sajeedGIT/shrike_lite_ssm/asset/reddit.png

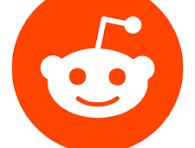
asset/reddit.png
