sajeedGIT/shrike_lite_ssm/asset/shrike_blink.webp

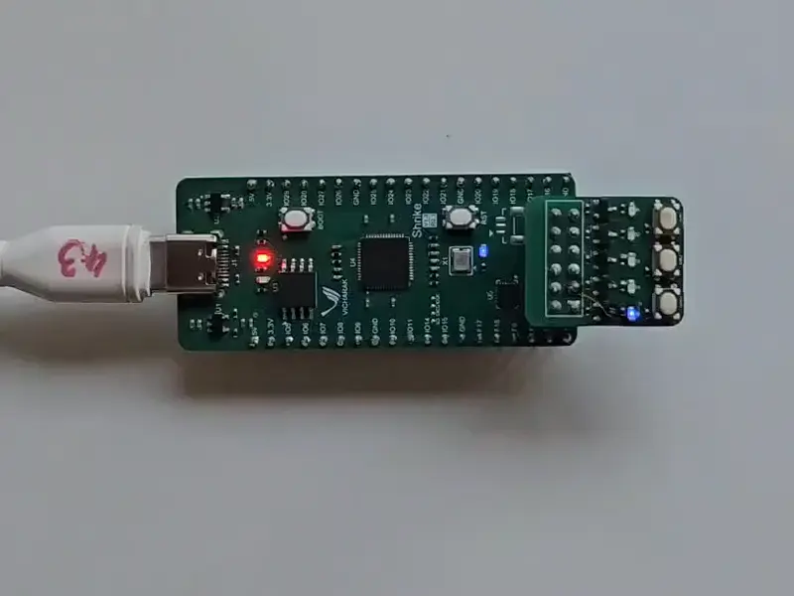
asset/shrike_blink.webp
