sajeedGIT/shrike_lite_ssm/asset/shrike_render.png

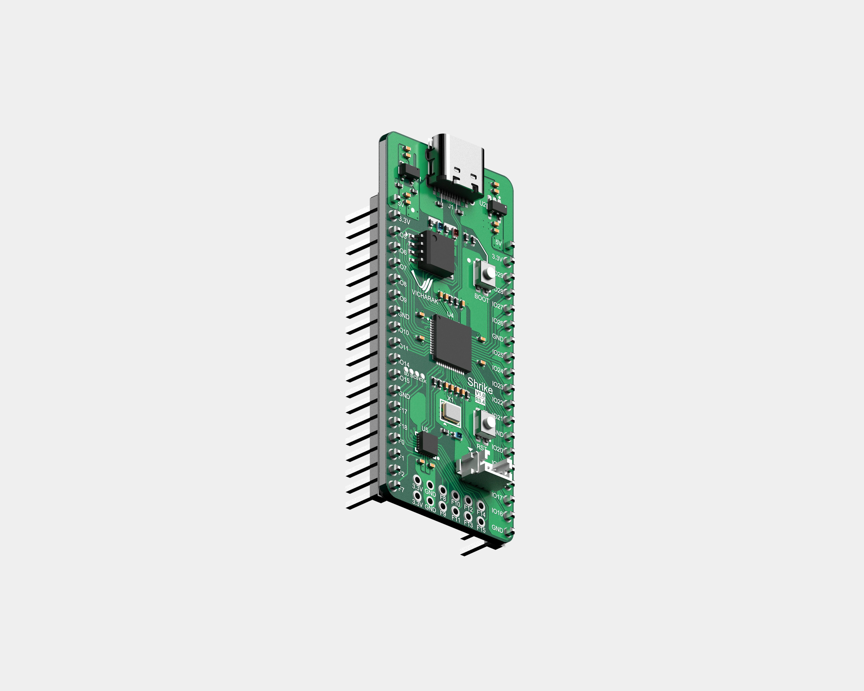
asset/shrike_render.png
