sajeedGIT/shrike_lite_ssm/docs/images/bit_stream.png

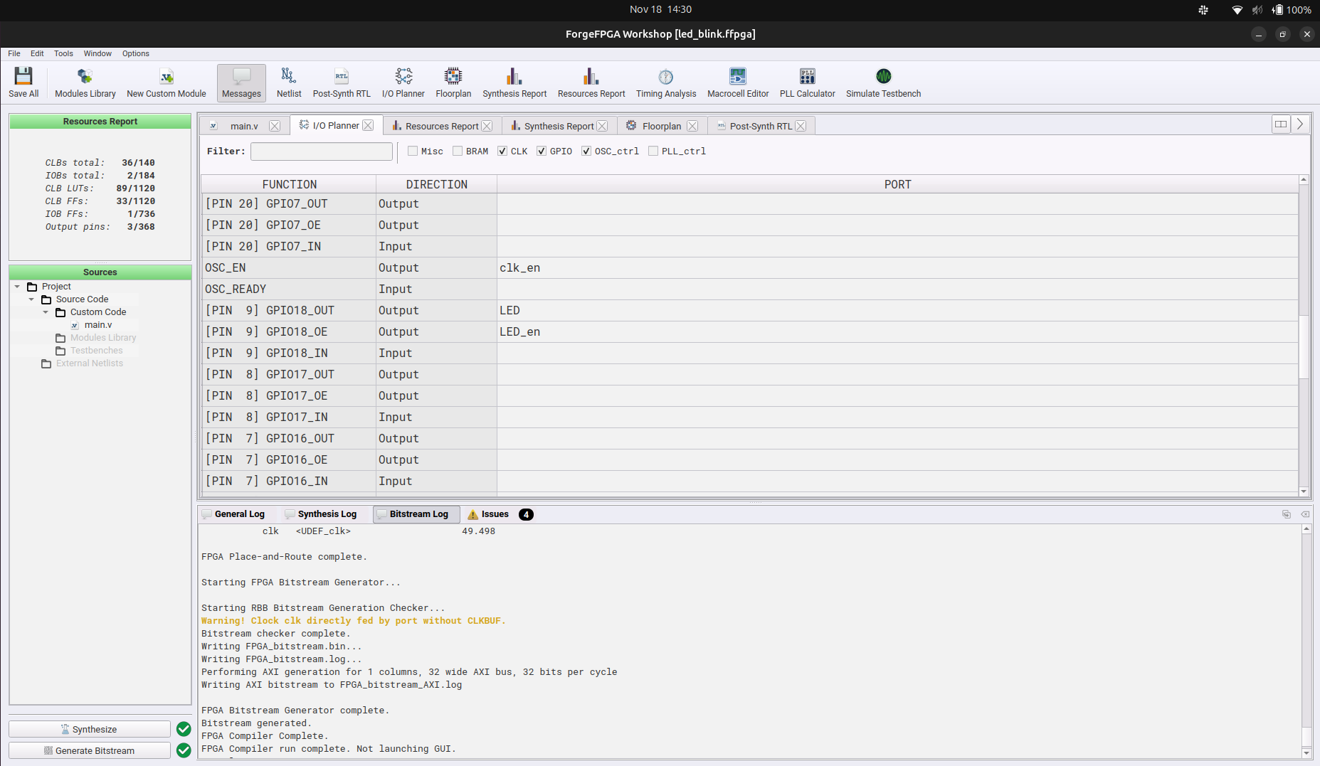
docs/images/bit_stream.png
