sajeedGIT/shrike_lite_ssm/docs/images/bitstream_gen/bitstream_done.png

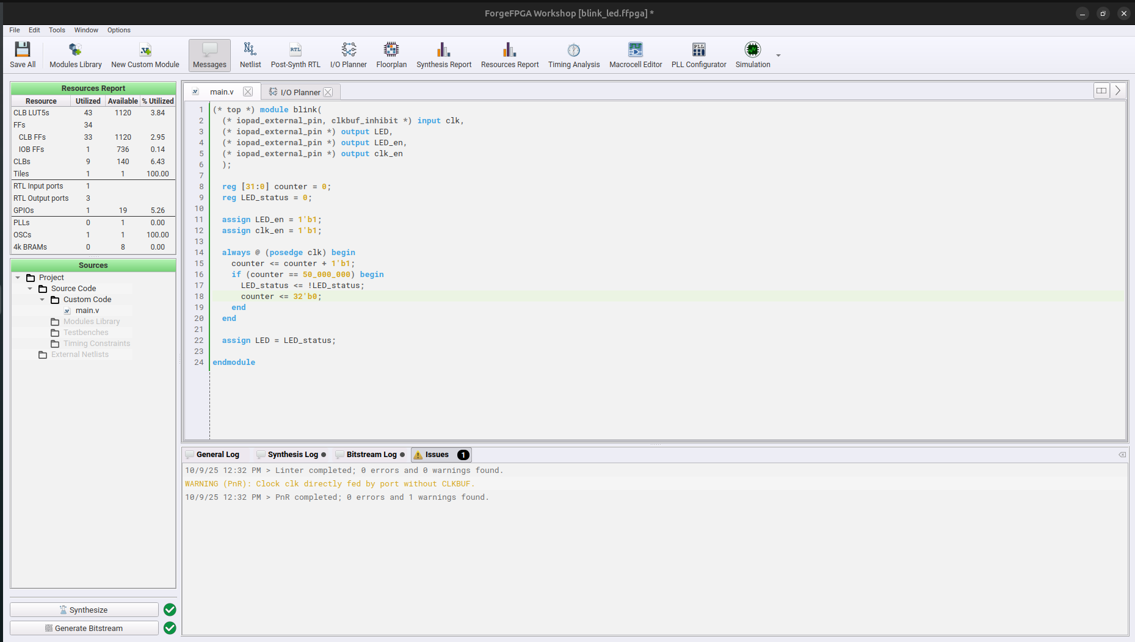
docs/images/bitstream_gen/bitstream_done.png
