sajeedGIT/shrike_lite_ssm/docs/images/bitstream_gen/clk_io.png

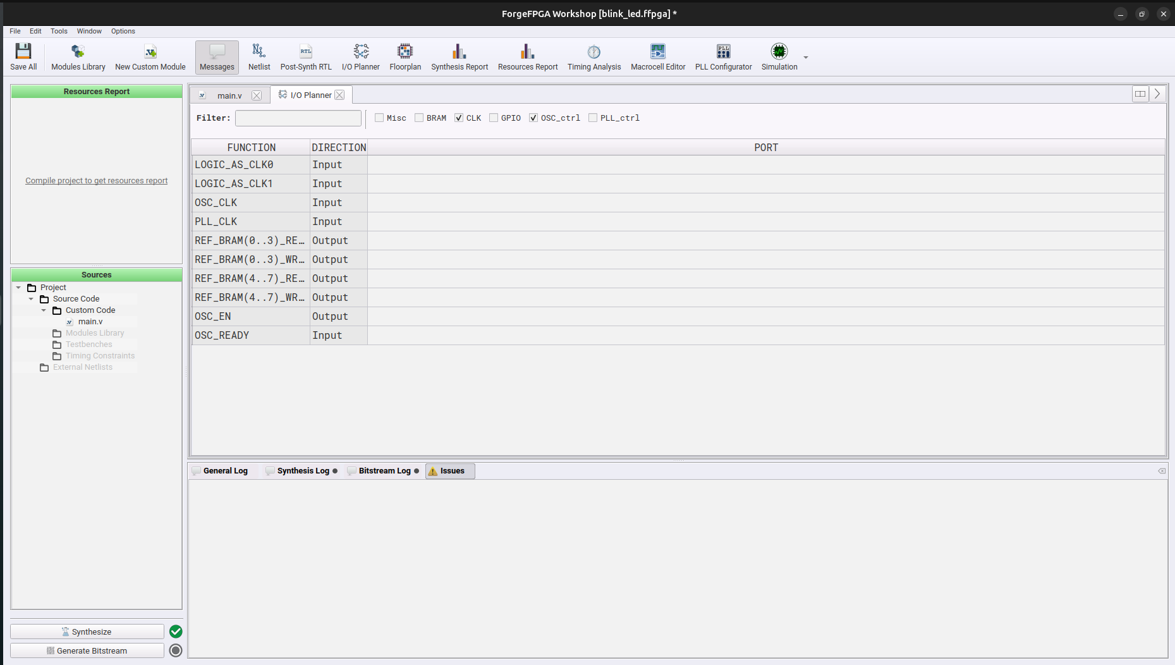
docs/images/bitstream_gen/clk_io.png
