sajeedGIT/shrike_lite_ssm/docs/images/bitstream_gen/empty_main.png

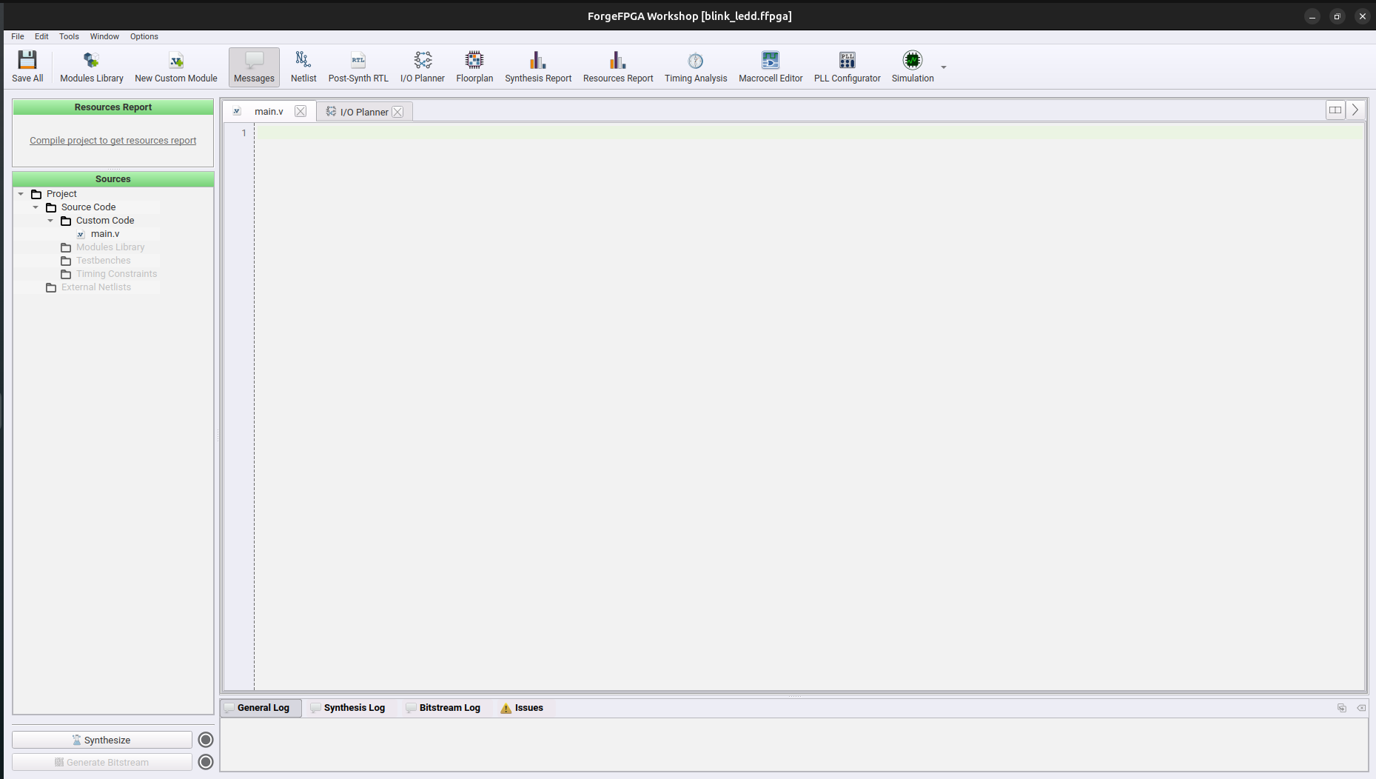
docs/images/bitstream_gen/empty_main.png
