sajeedGIT/shrike_lite_ssm/docs/images/bitstream_gen/fpga_selection.png

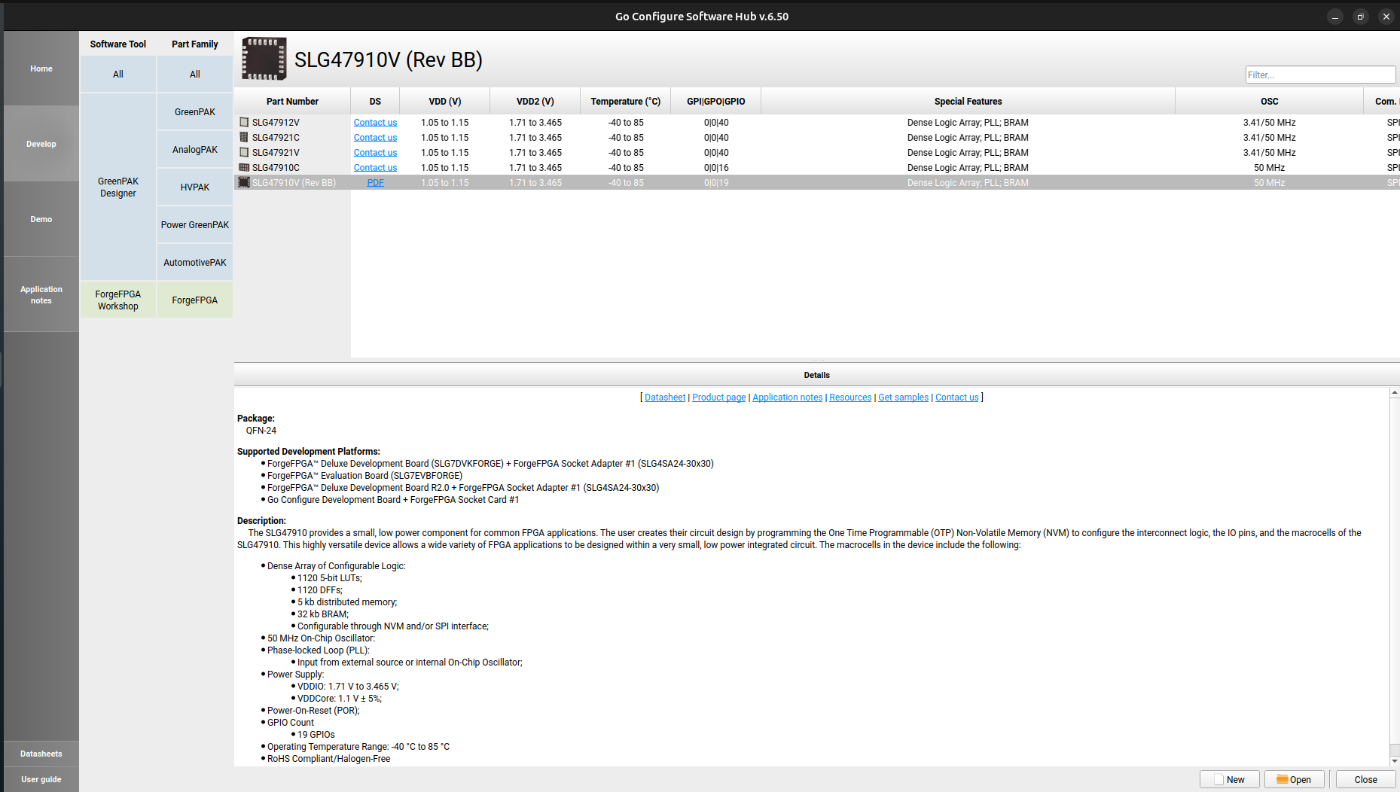
docs/images/bitstream_gen/fpga_selection.png
