sajeedGIT/shrike_lite_ssm/docs/images/bitstream_gen/fpgacore.png

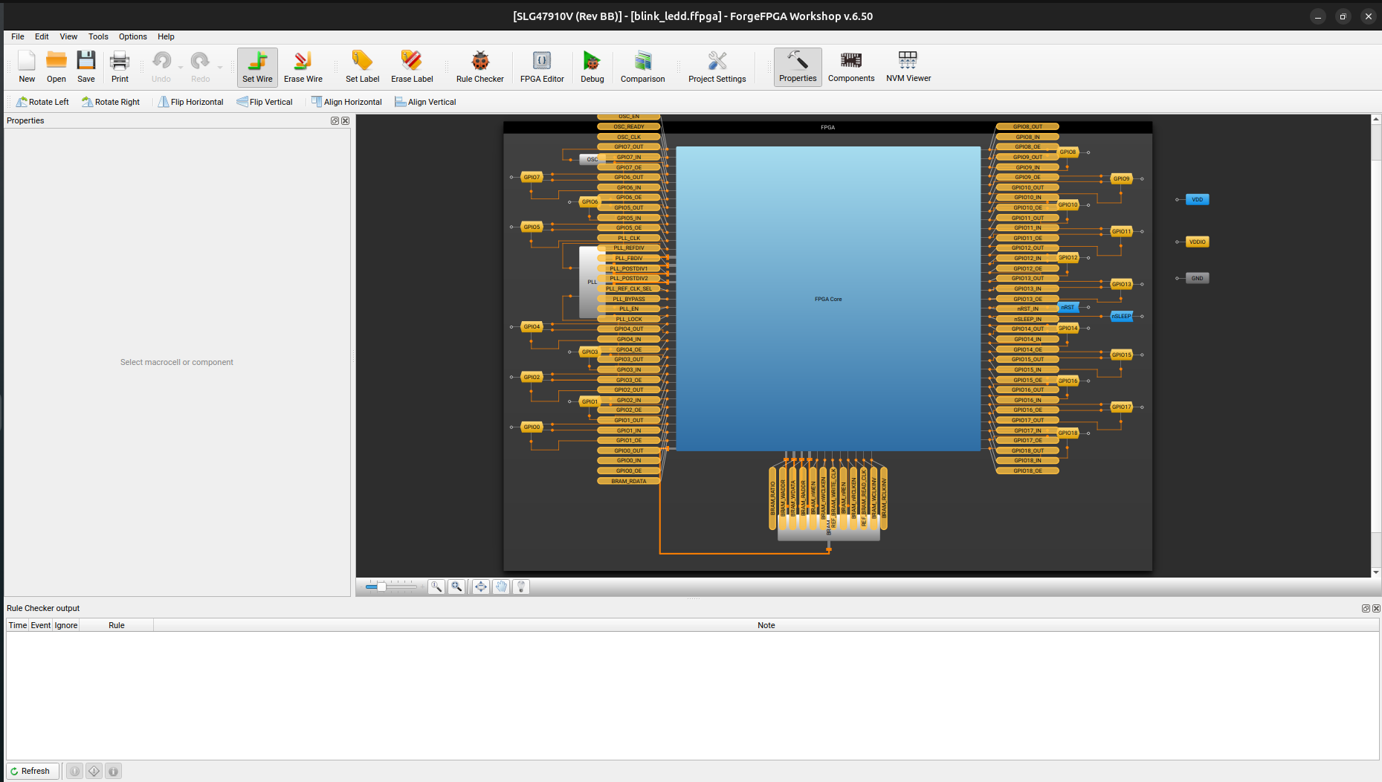
docs/images/bitstream_gen/fpgacore.png
