sajeedGIT/shrike_lite_ssm/docs/images/bitstream_gen/go_config_launch.png

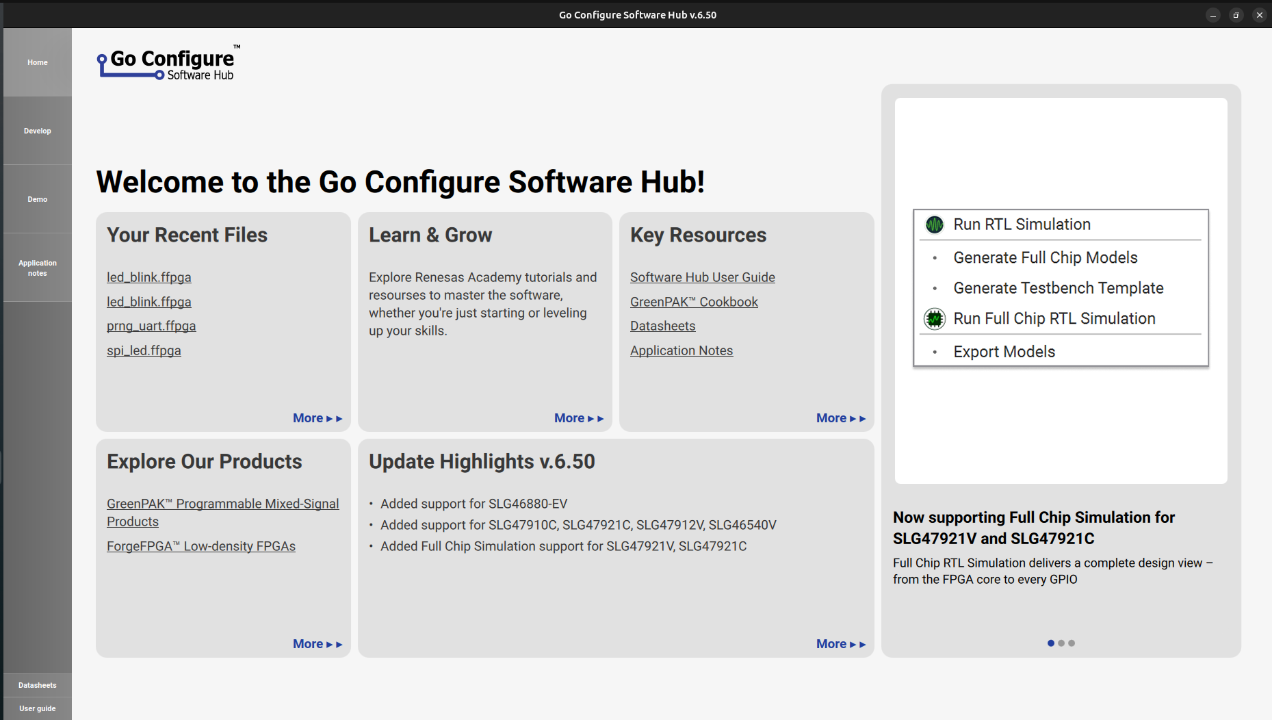
docs/images/bitstream_gen/go_config_launch.png
