sajeedGIT/shrike_lite_ssm/docs/images/bitstream_gen/io_planner.png

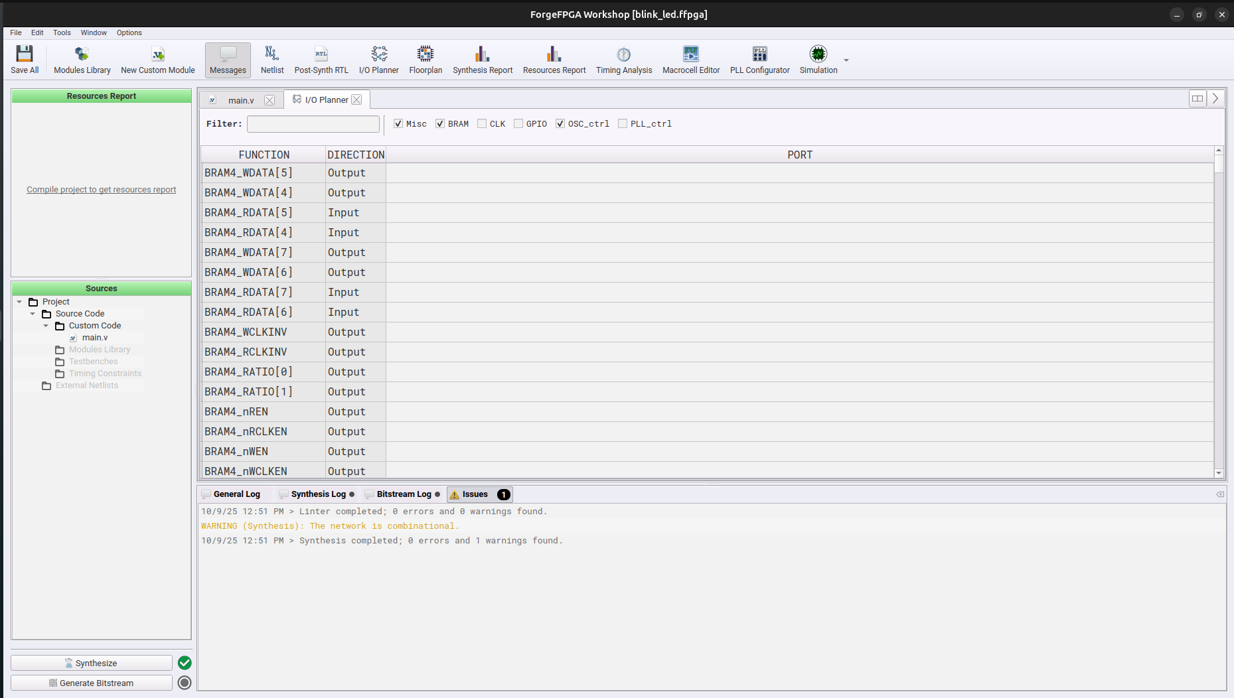
docs/images/bitstream_gen/io_planner.png
