sajeedGIT/shrike_lite_ssm/docs/images/bitstream_gen/led_io_map.png

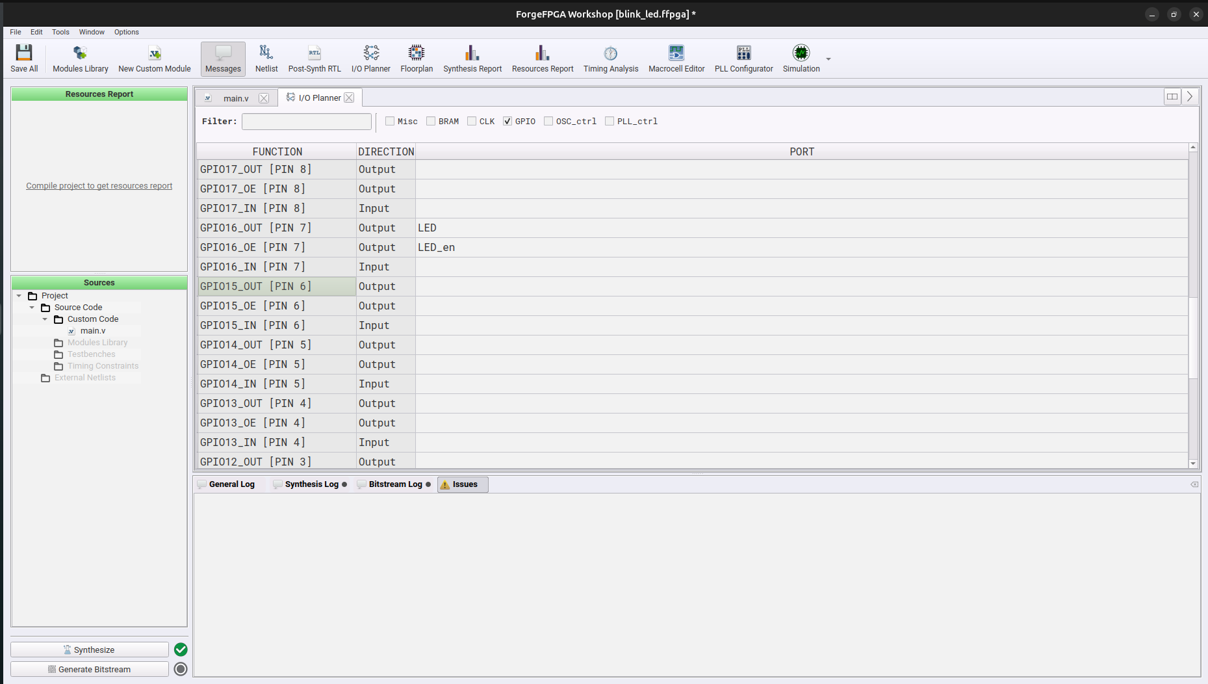
docs/images/bitstream_gen/led_io_map.png
