sajeedGIT/shrike_lite_ssm/docs/images/bitstream_gen/mainv_code.png

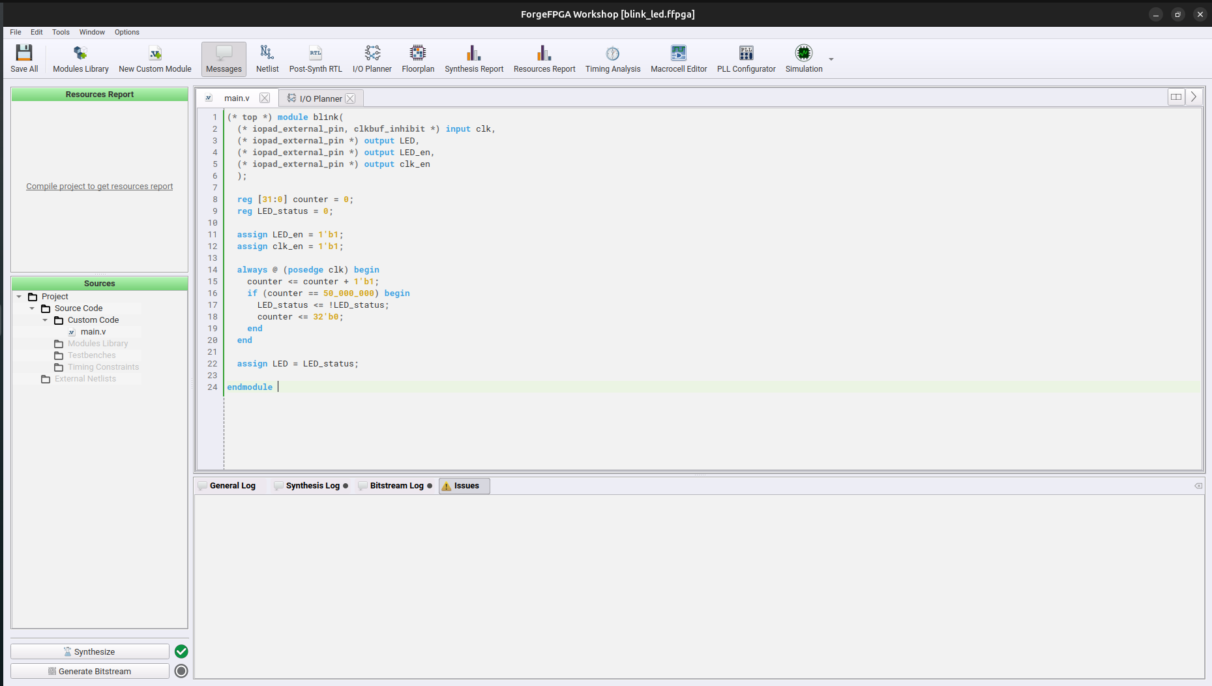
docs/images/bitstream_gen/mainv_code.png
