sajeedGIT/shrike_lite_ssm/docs/images/bitstream_gen/project_path.png

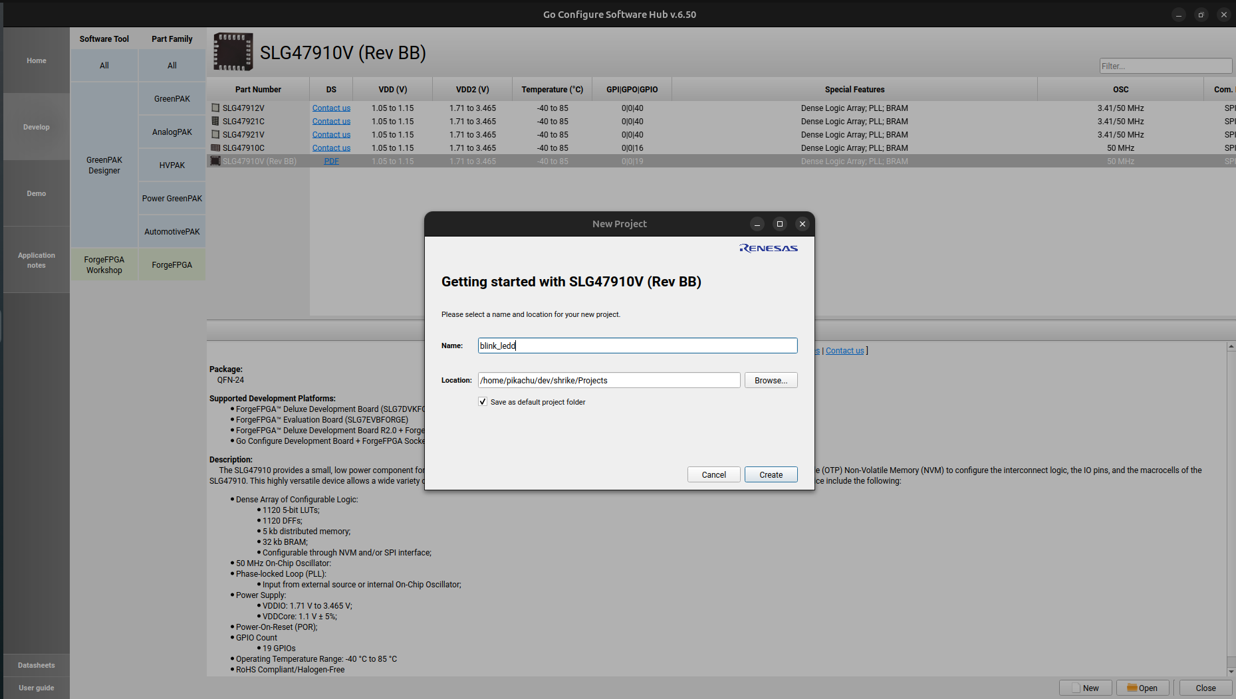
docs/images/bitstream_gen/project_path.png
