sajeedGIT/shrike_lite_ssm/docs/images/bitstream_gen/project_setting.png

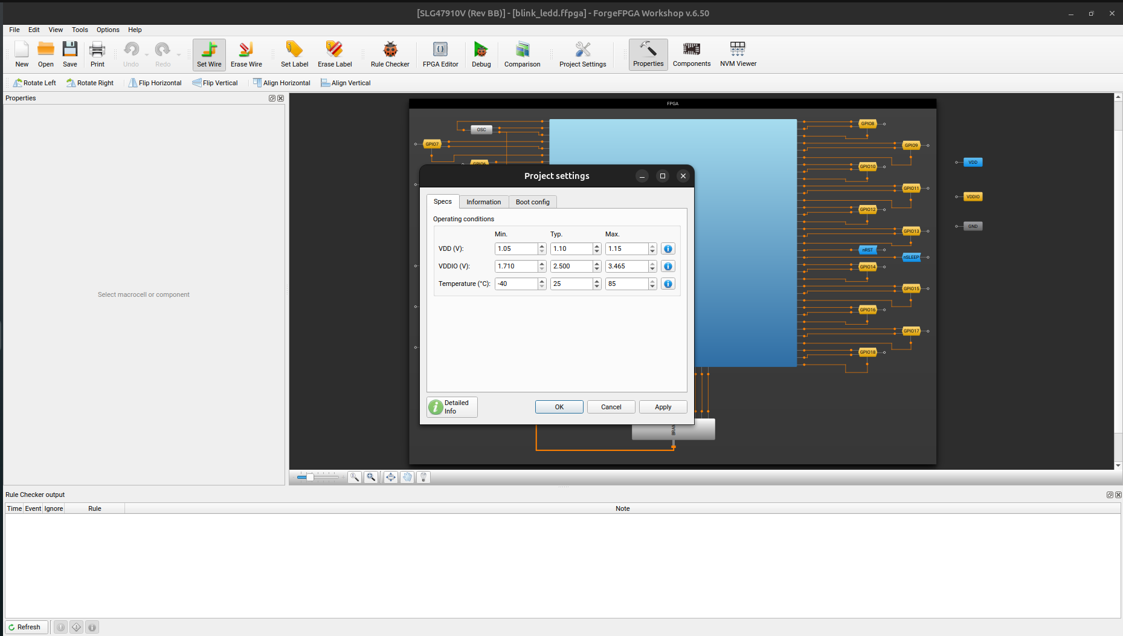
docs/images/bitstream_gen/project_setting.png
