sajeedGIT/shrike_lite_ssm/docs/images/clk.png

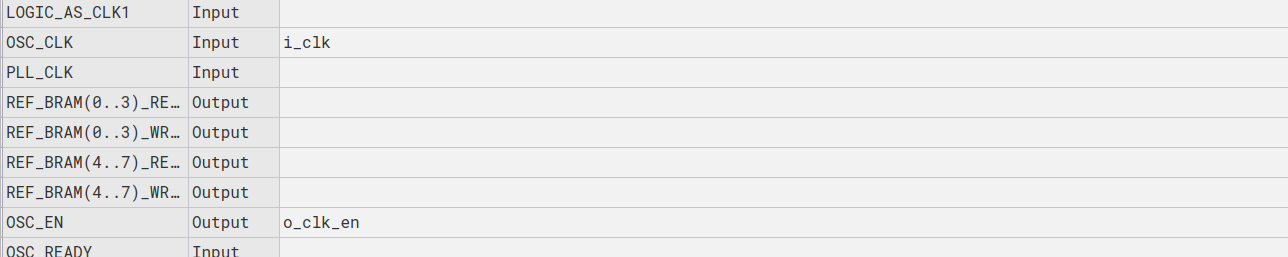
docs/images/clk.png
