sajeedGIT/shrike_lite_ssm/docs/images/code_entry.png

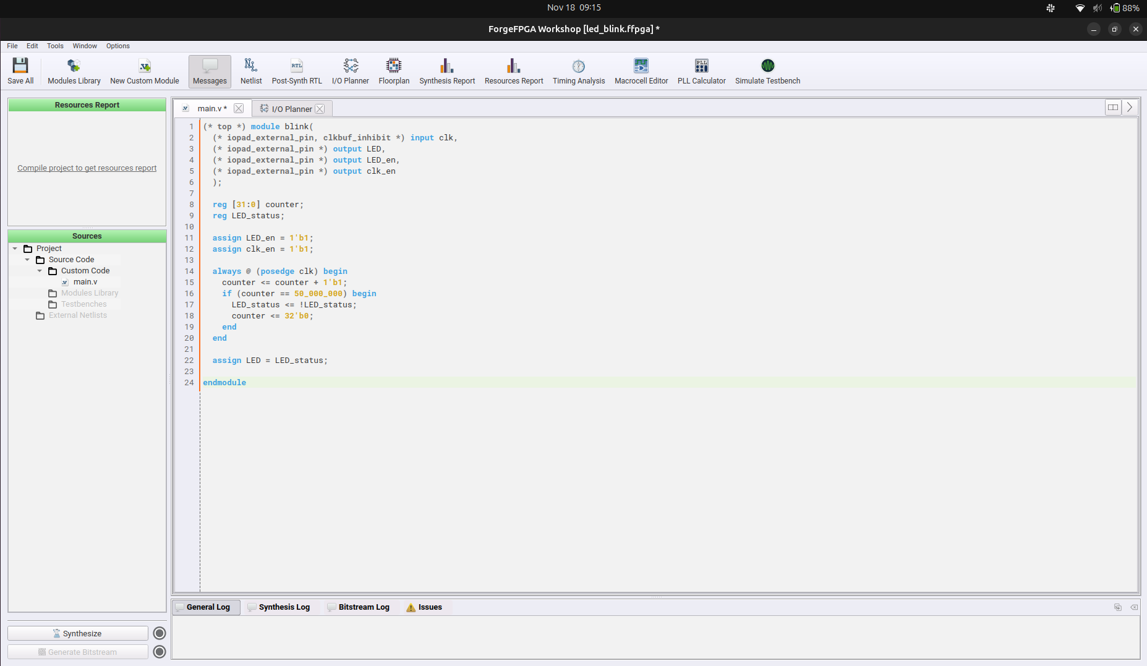
docs/images/code_entry.png
