sajeedGIT/shrike_lite_ssm/docs/images/done.png

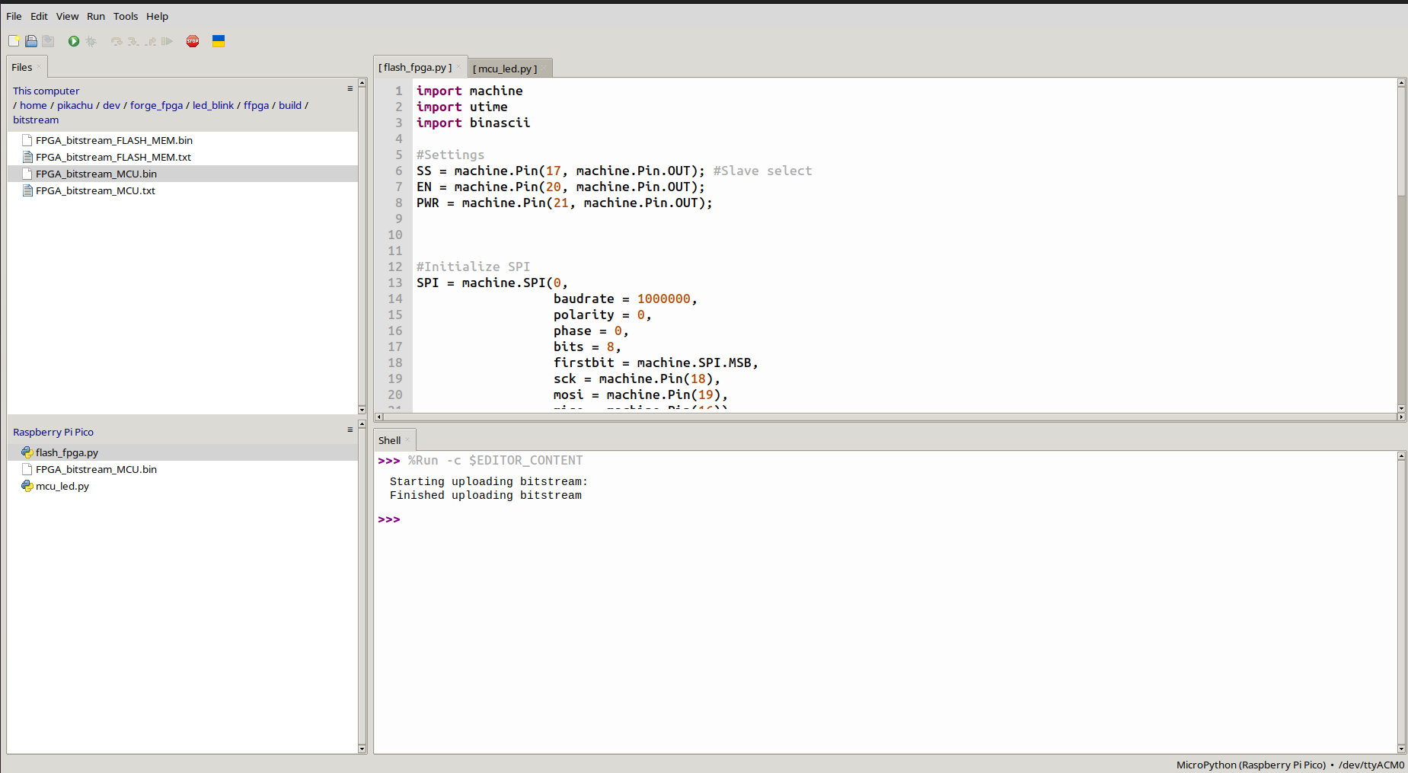
docs/images/done.png
