sajeedGIT/shrike_lite_ssm/docs/images/downlode.png

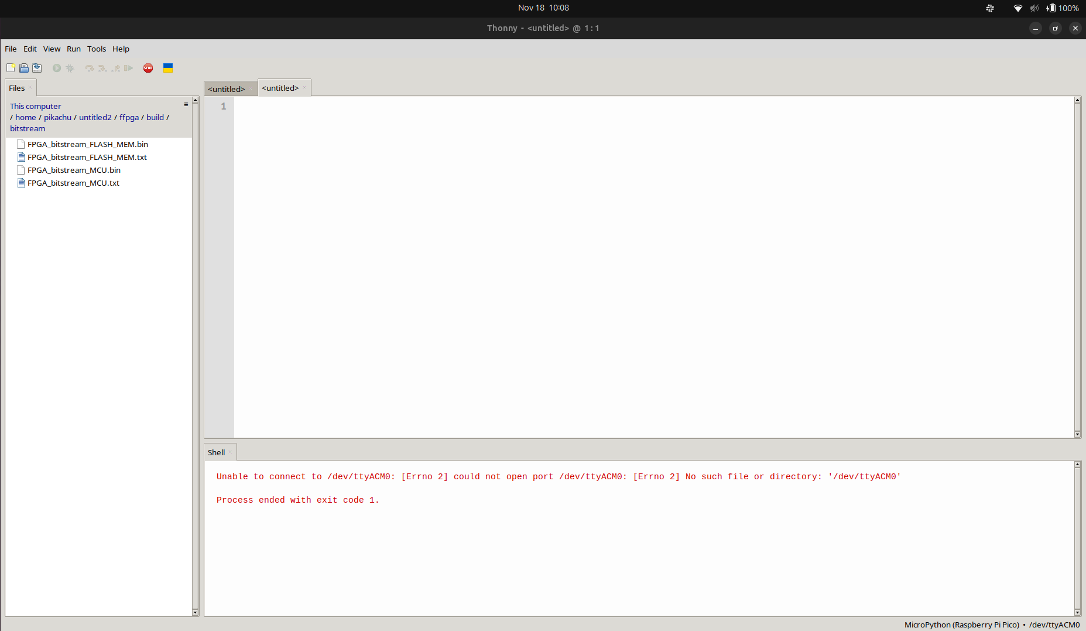
docs/images/downlode.png
