sajeedGIT/shrike_lite_ssm/docs/images/forge_fpga_workshop.png

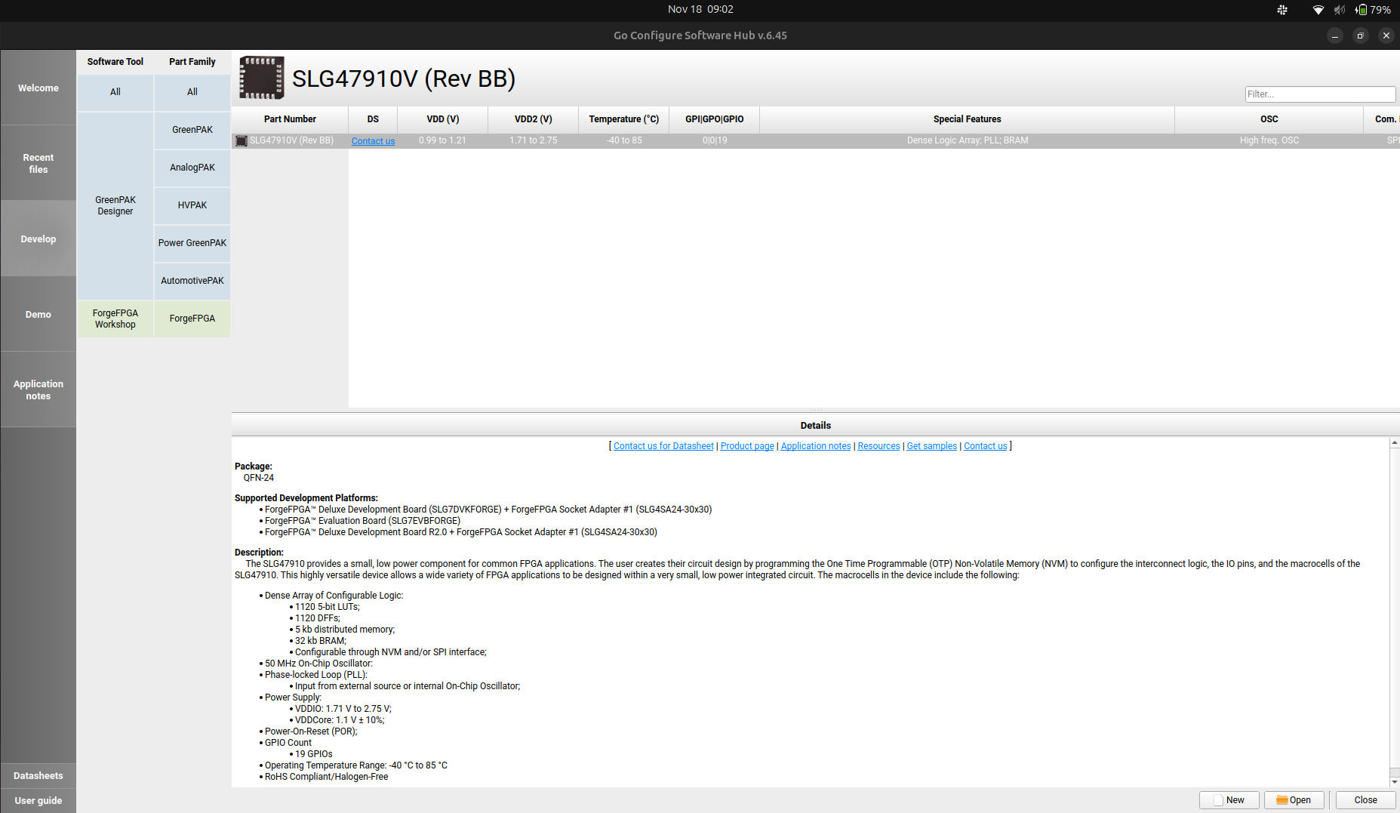
docs/images/forge_fpga_workshop.png
