sajeedGIT/shrike_lite_ssm/docs/images/go_configure_startup.png

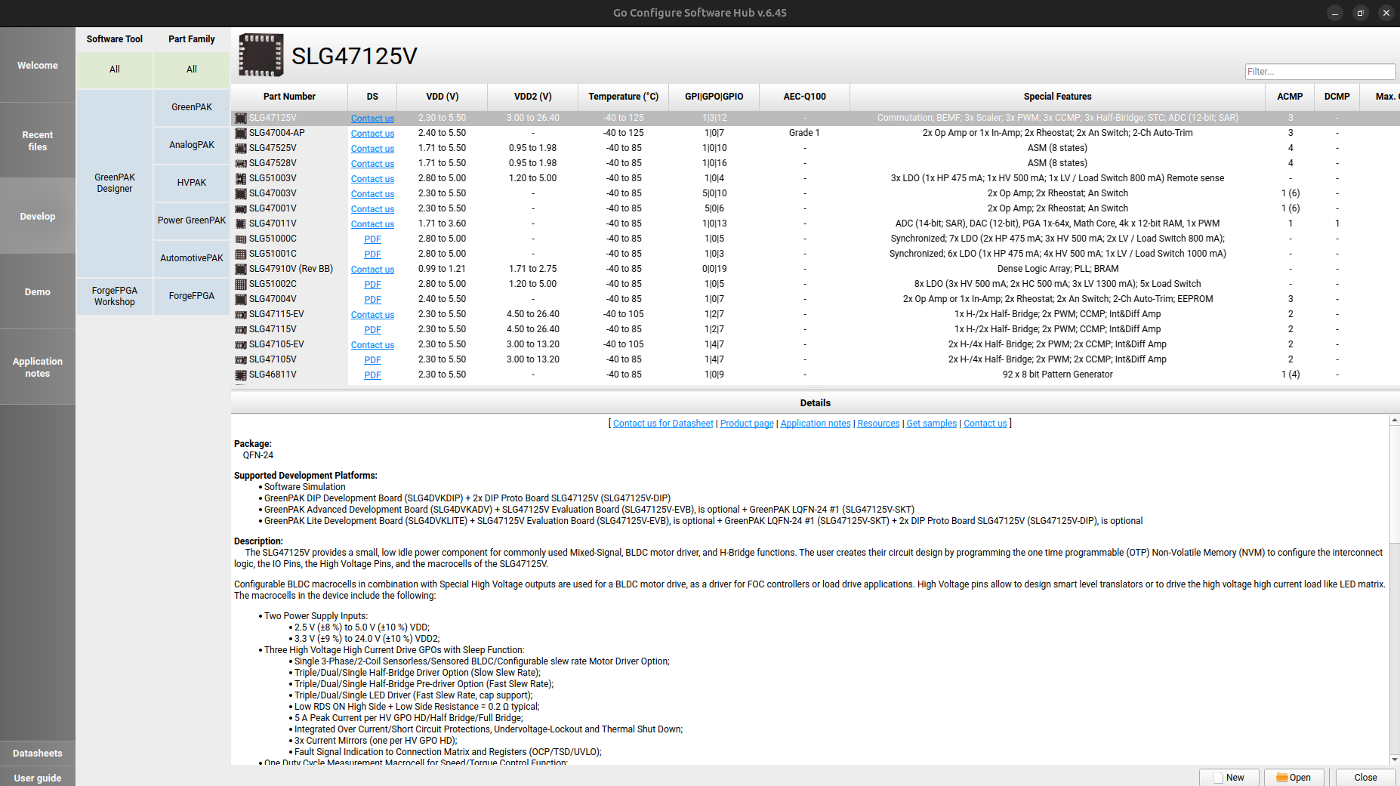
docs/images/go_configure_startup.png
