sajeedGIT/shrike_lite_ssm/docs/images/ide_home.png

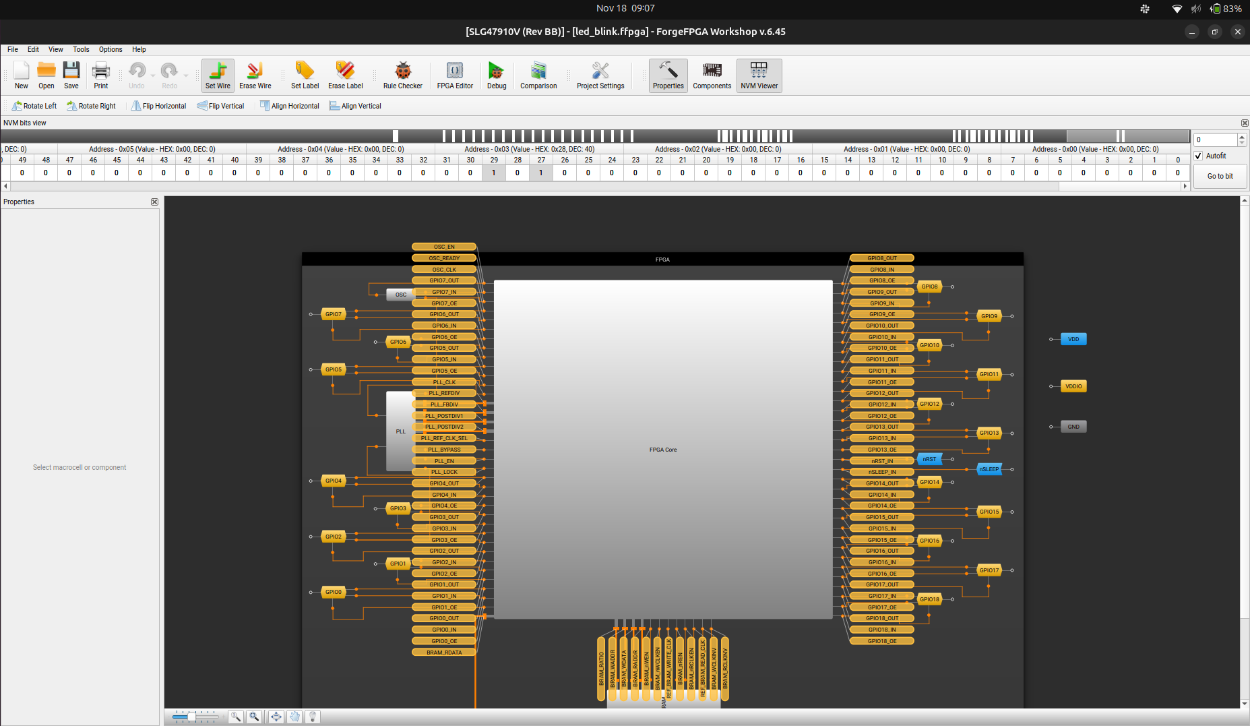
docs/images/ide_home.png
