sajeedGIT/shrike_lite_ssm/docs/images/log_in.png

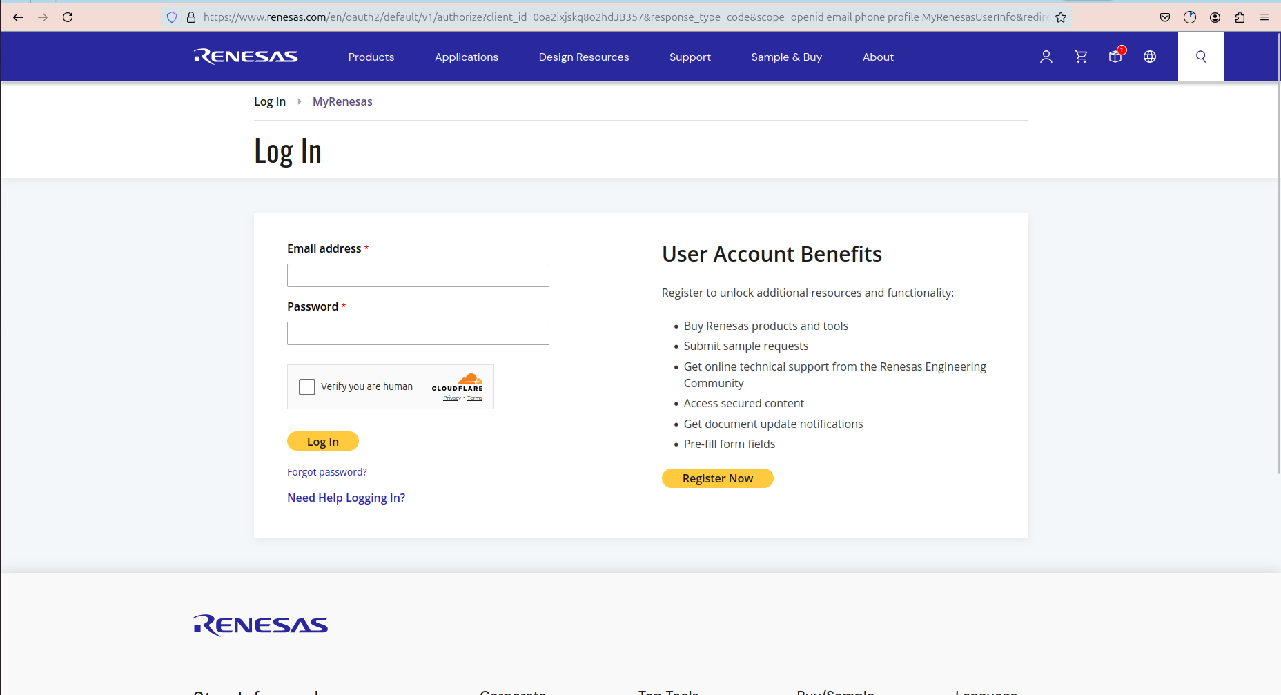
docs/images/log_in.png
