sajeedGIT/shrike_lite_ssm/docs/images/main_v.png

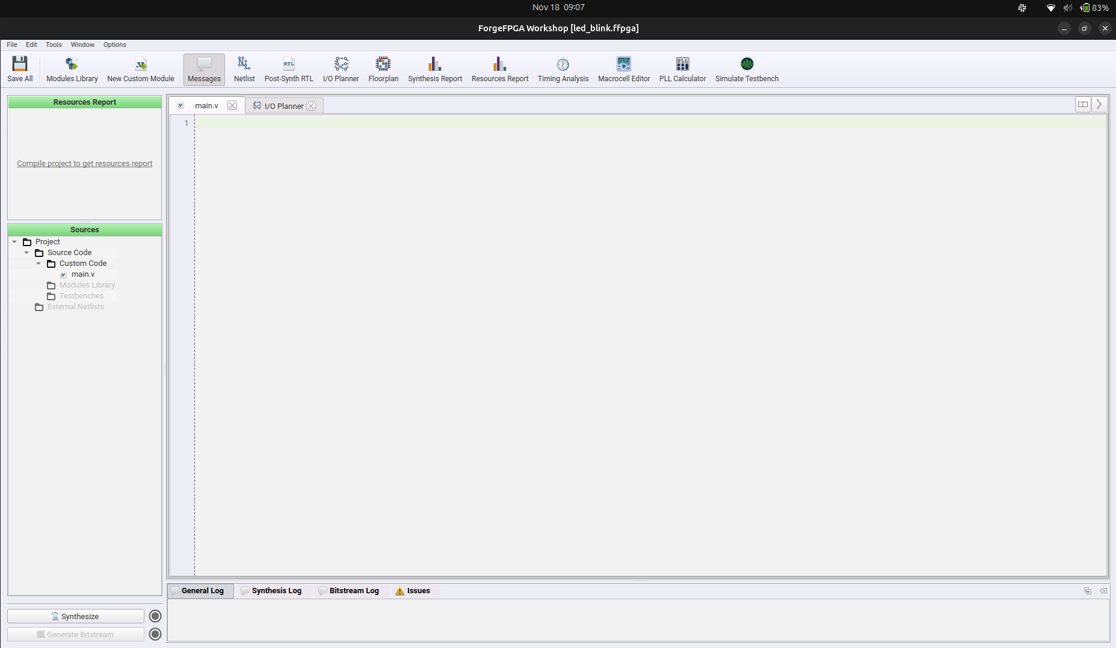
docs/images/main_v.png
