sajeedGIT/shrike_lite_ssm/docs/images/os.png

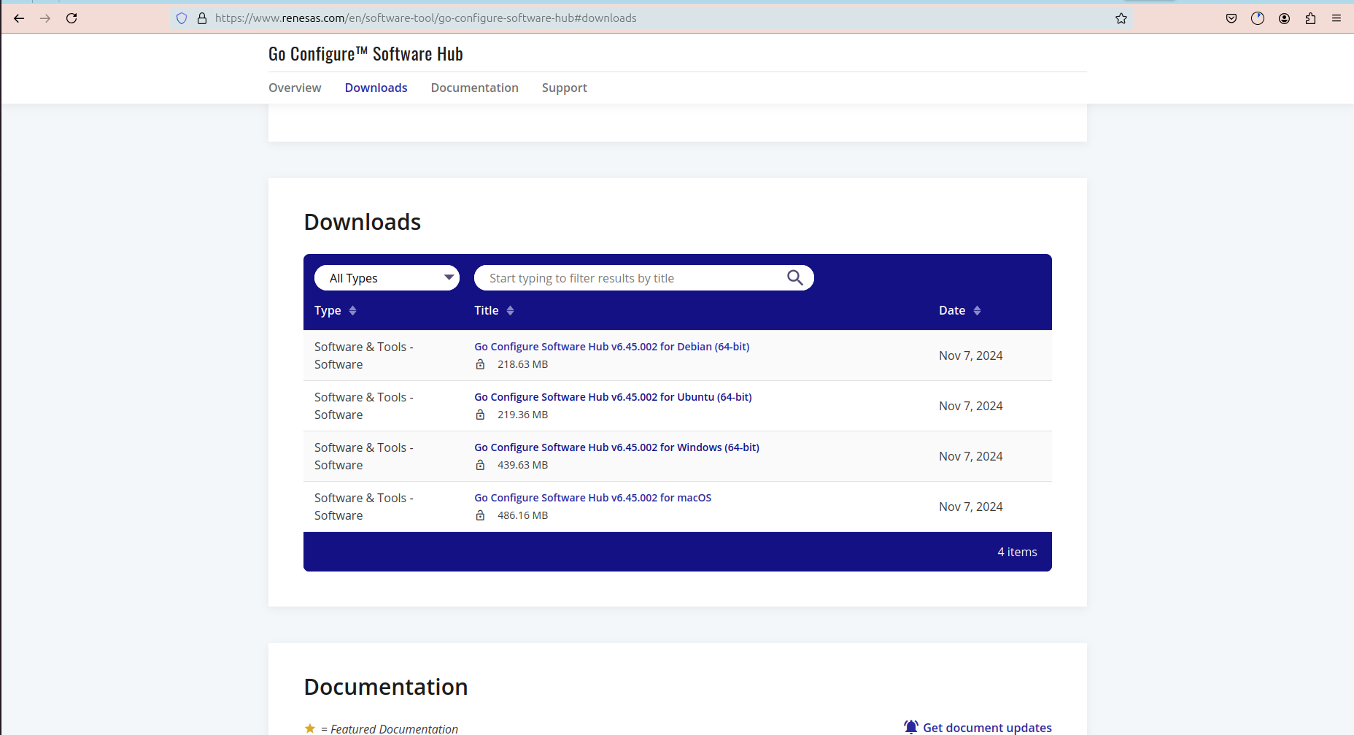
docs/images/os.png
