sajeedGIT/shrike_lite_ssm/docs/images/proejct_properties.png

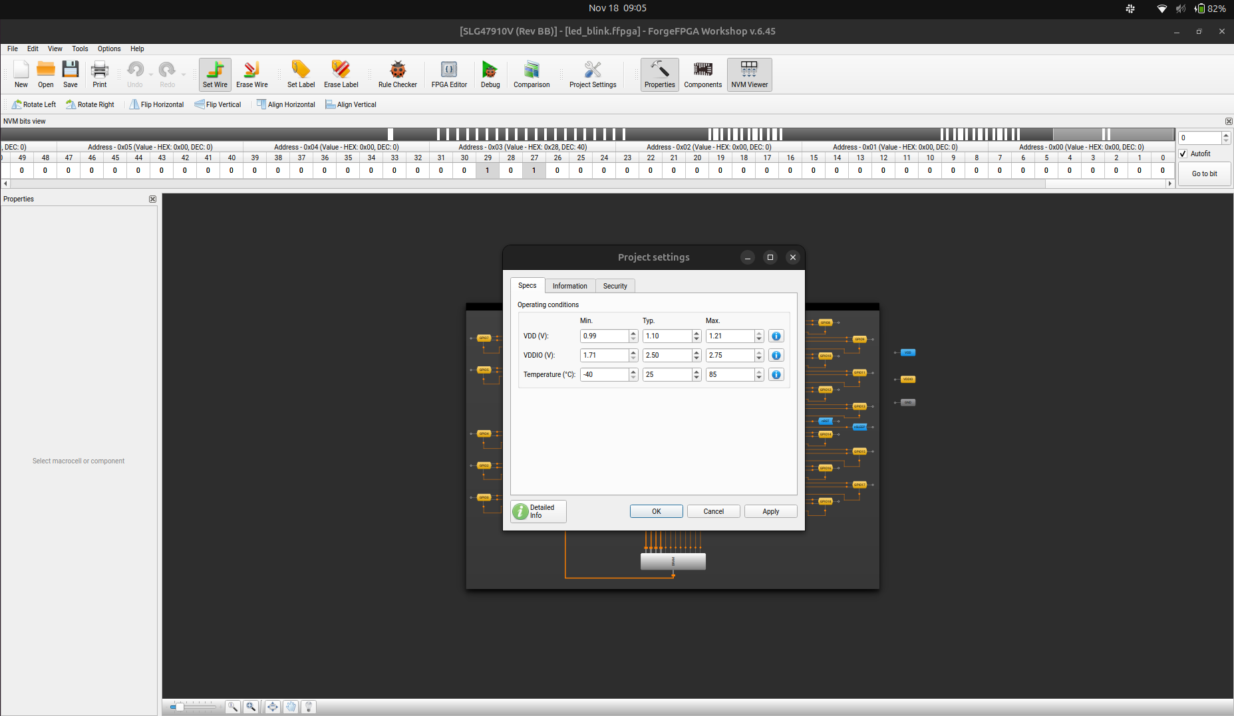
docs/images/proejct_properties.png
