sajeedGIT/shrike_lite_ssm/docs/images/project_navigation.png

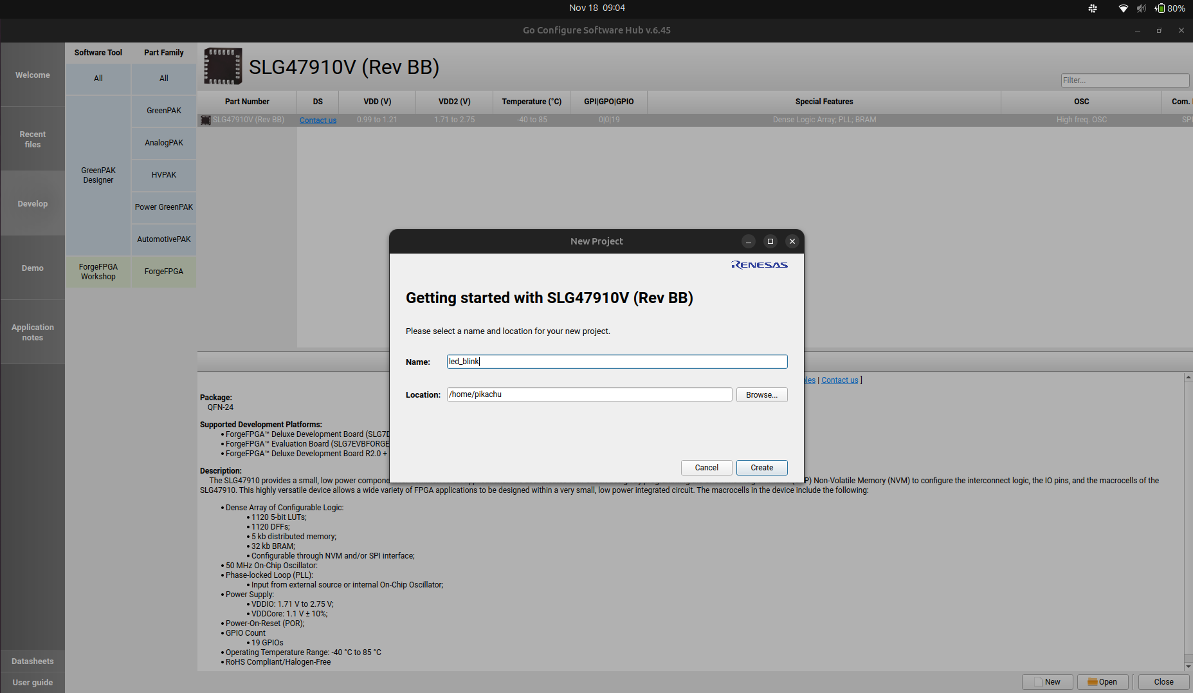
docs/images/project_navigation.png
