sajeedGIT/shrike_lite_ssm/docs/images/shrike_block_dia.png

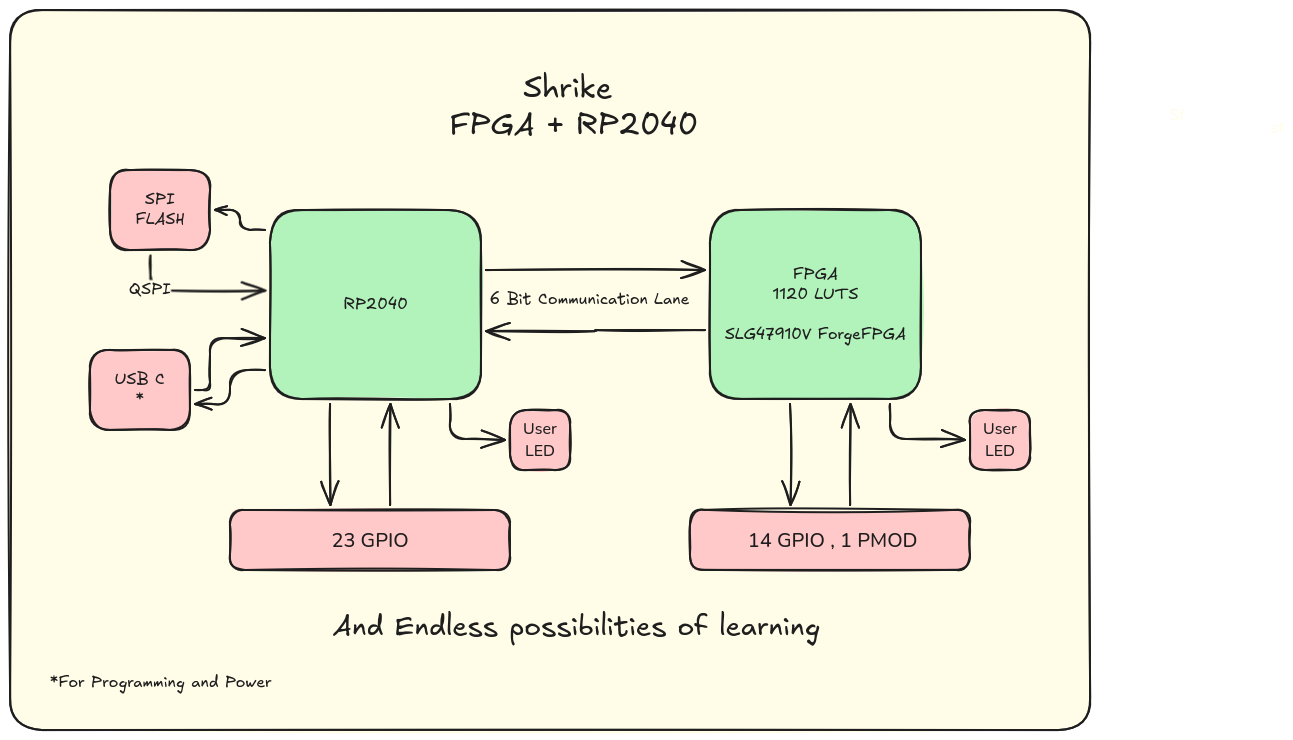
docs/images/shrike_block_dia.png
