sajeedGIT/shrike_lite_ssm/docs/images/Shrike_with_pmod.jpeg

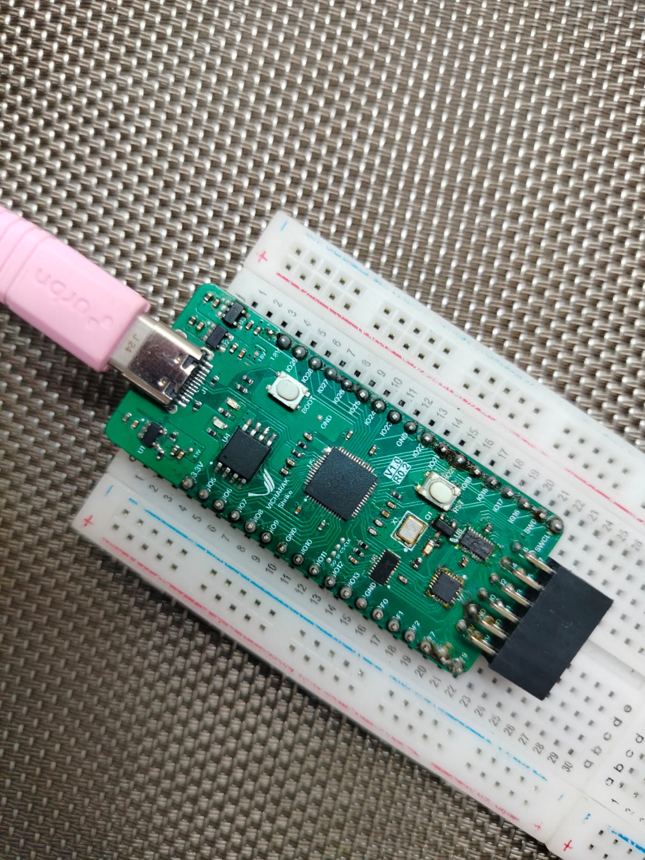
docs/images/Shrike_with_pmod.jpeg
