sajeedGIT/shrike_lite_ssm/docs/images/synthesize.png

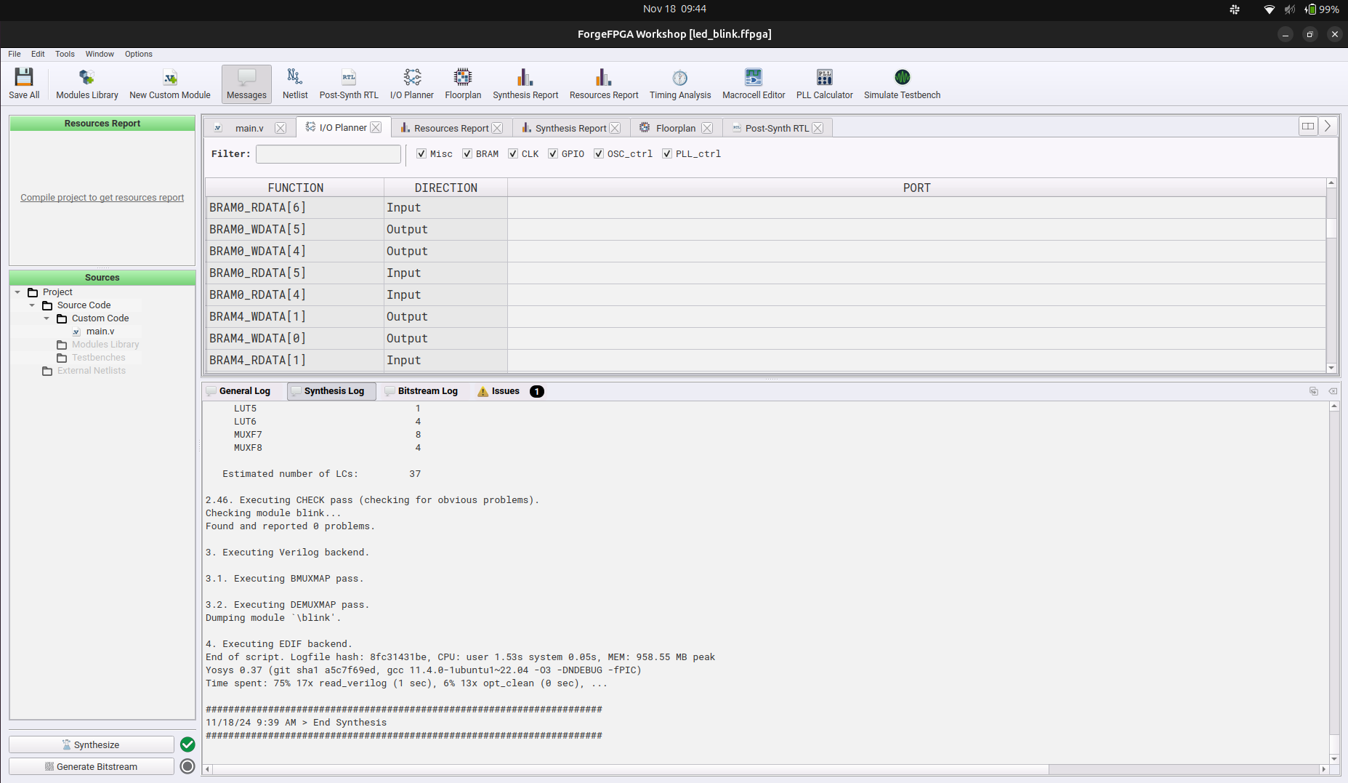
docs/images/synthesize.png
