sajeedGIT/shrike_lite_ssm/docs/images/Thonny_main.png

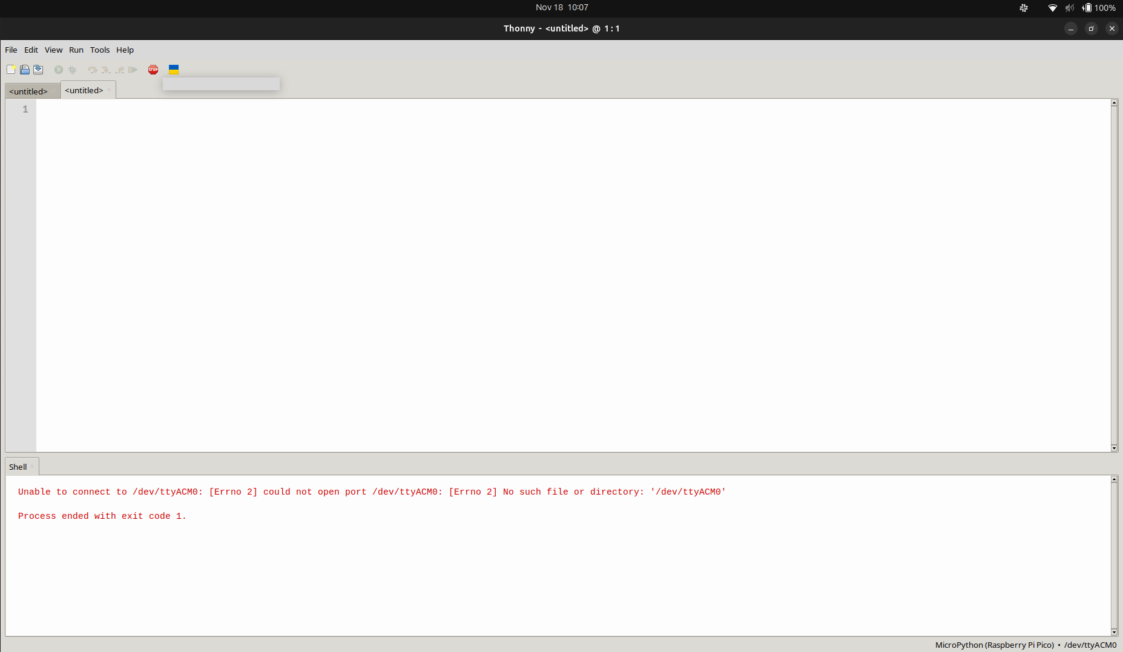
docs/images/Thonny_main.png
