sajeedGIT/shrike_lite_ssm/docs/images/uplode.png

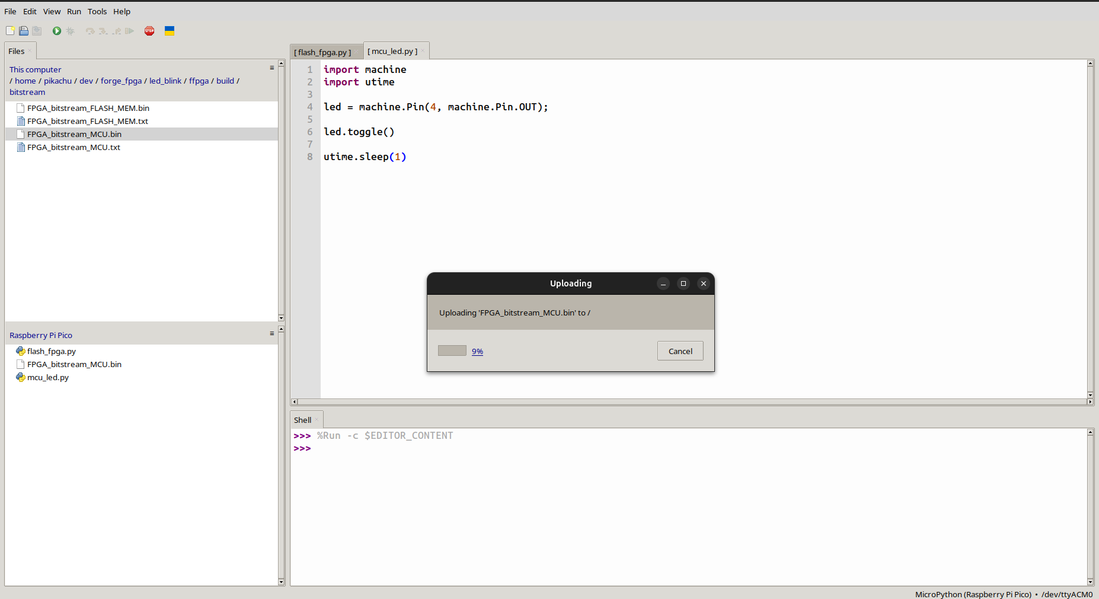
docs/images/uplode.png
