sajeedGIT/shrike_lite_ssm/examples/counter_4bit/media/4Bit_UpDown_Counter.png

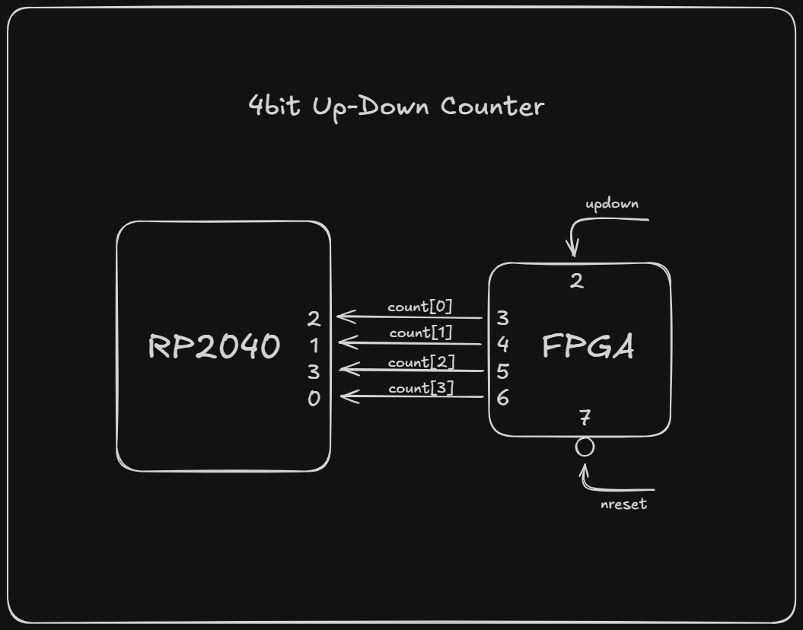
examples/counter_4bit/media/4Bit_UpDown_Counter.png
