sajeedGIT/shrike_lite_ssm/examples/dspi_pio_echo/images/dspi_bus_output.png

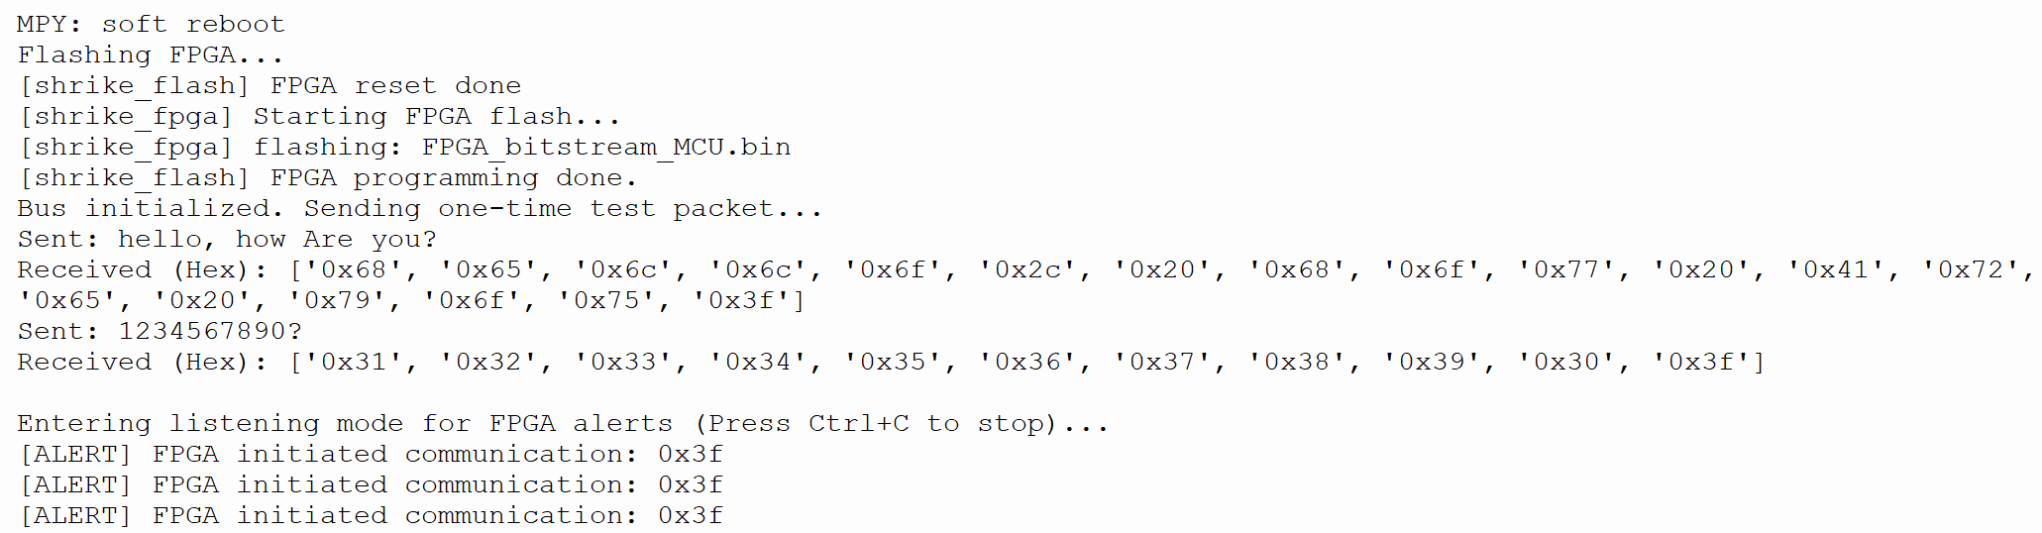
examples/dspi_pio_echo/images/dspi_bus_output.png
