sajeedGIT/shrike_lite_ssm/examples/protocol_translator/uart_to_spi_bridge/images/block_diagram.png

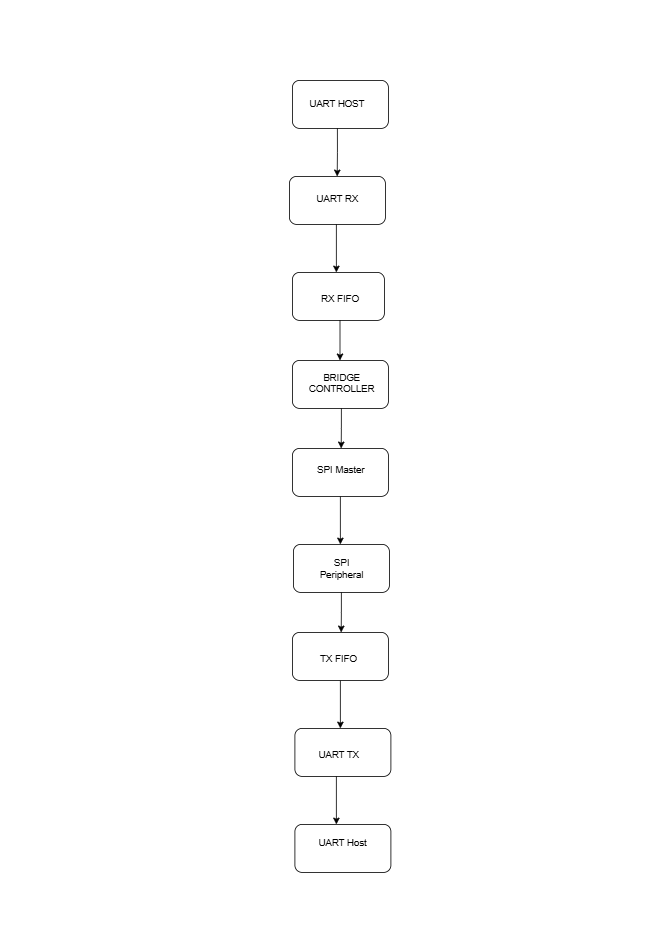
examples/protocol_translator/uart_to_spi_bridge/images/block_diagram.png
