sajeedGIT/shrike_lite_ssm/examples/quadrature_decoder/ffpga/images/quadrature_decoder_blockdiagram.png

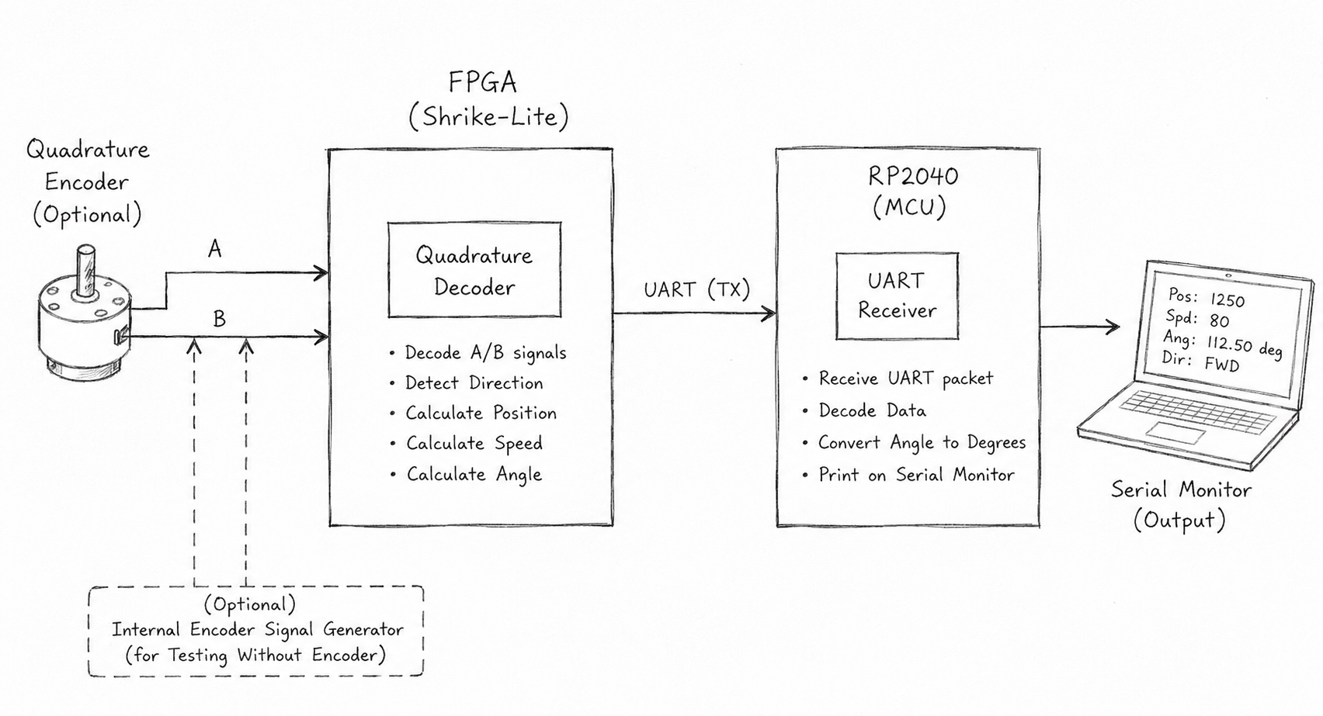
examples/quadrature_decoder/ffpga/images/quadrature_decoder_blockdiagram.png
