sajeedGIT/shrike_lite_ssm/examples/quadrature_decoder/ffpga/images/quadrature_decoder_output.png

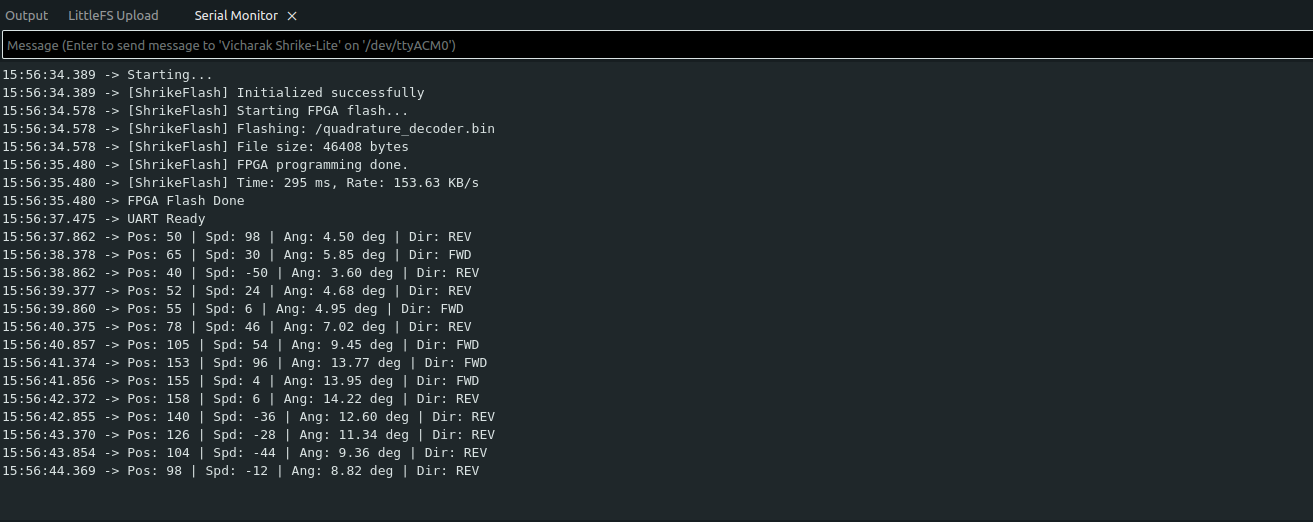
examples/quadrature_decoder/ffpga/images/quadrature_decoder_output.png
