sajeedGIT/shrike_lite_ssm/examples/stack_processor/assets/images/bram0_fp.JPG

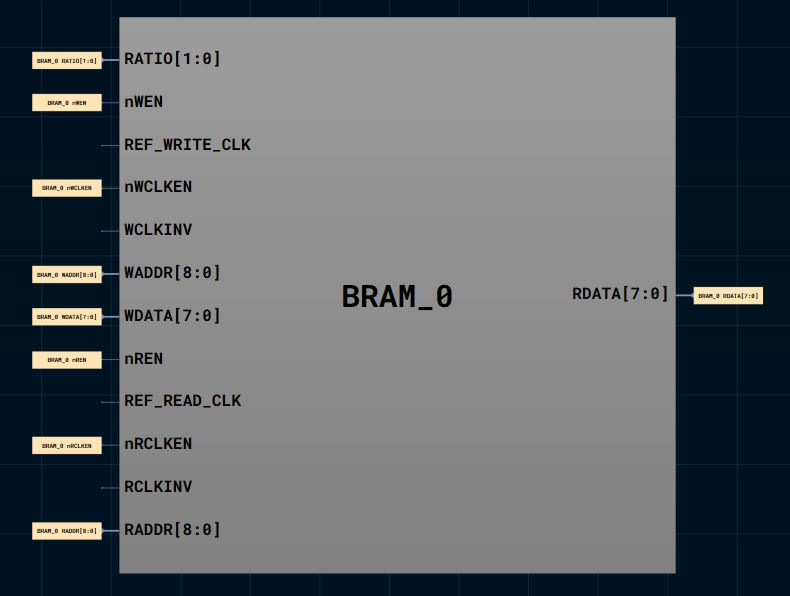
examples/stack_processor/assets/images/bram0_fp.JPG
