sajeedGIT/shrike_lite_ssm/examples/stack_processor/assets/images/bram_en.JPG

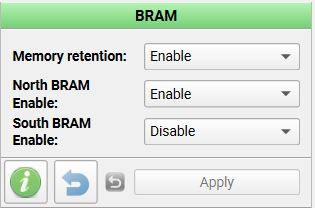
examples/stack_processor/assets/images/bram_en.JPG
