sajeedGIT/shrike_lite_ssm/examples/uart_sum/ffpga/images/output.JPG

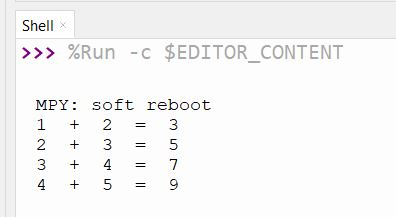
examples/uart_sum/ffpga/images/output.JPG
