sajeedGIT/shrike_lite_ssm/examples/usb_to_spi/images/received_data.jpeg

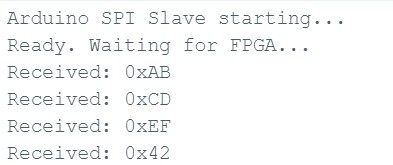
examples/usb_to_spi/images/received_data.jpeg
