sajeedGIT/shrike_lite_ssm/examples/usb_to_spi/images/transmitted_data.jpeg

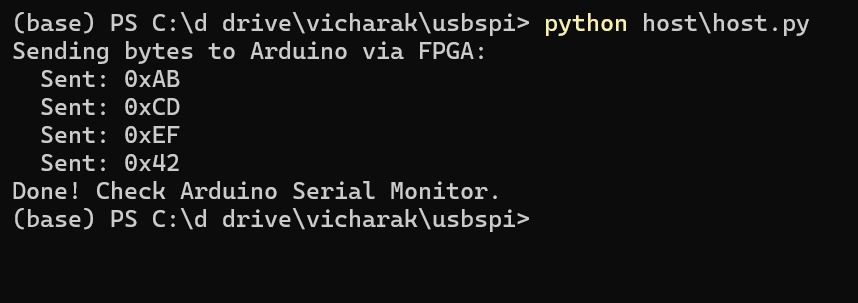
examples/usb_to_spi/images/transmitted_data.jpeg
