sajeedGIT/shrike_lite_ssm/utils/shrike-fi_web_flasher/_assests/web_flash_ui.png

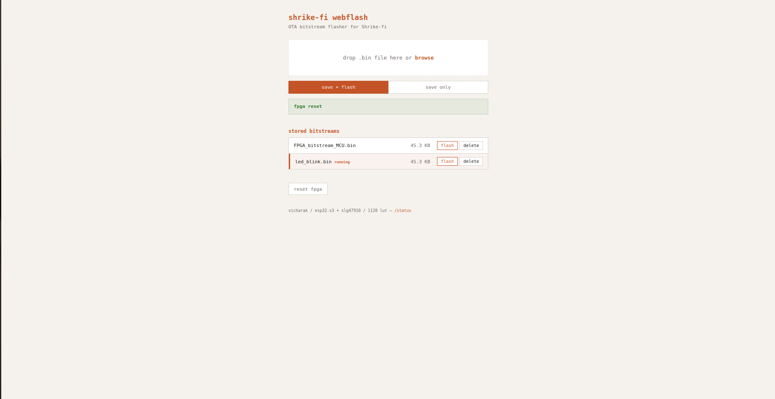
utils/shrike-fi_web_flasher/_assests/web_flash_ui.png
