sajeedGIT/shrike_lite_ssm/utils/shrike-fi_web_flasher/arduino-ide/images/Output.png

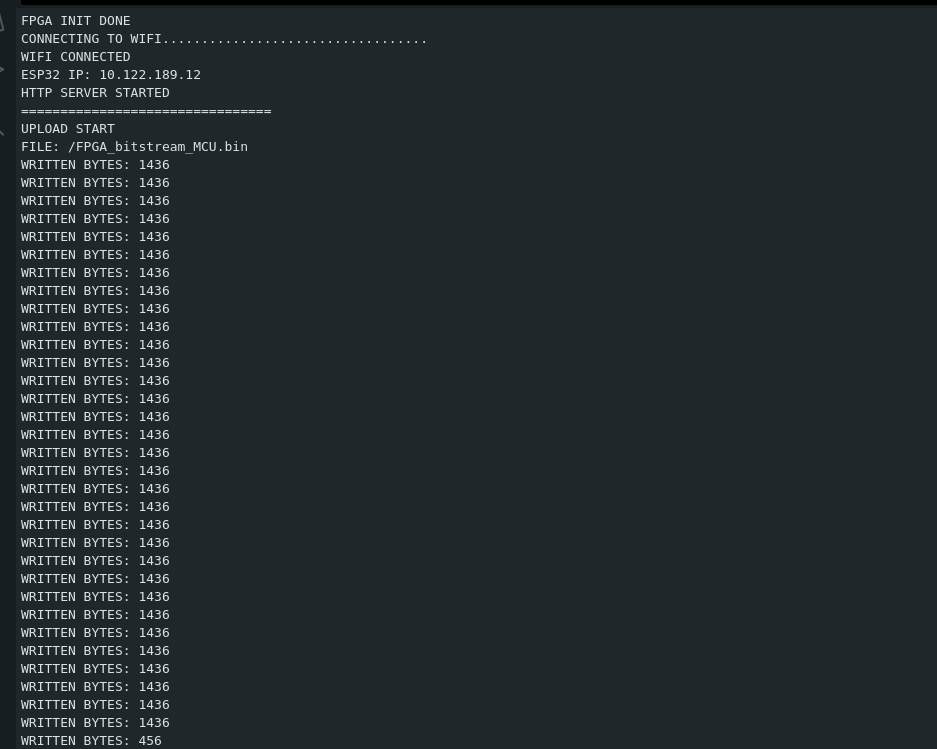
utils/shrike-fi_web_flasher/arduino-ide/images/Output.png
