sajeedGIT/shrike_lite_ssm/docs/images/tools_setup/goconfig_landing_page.png

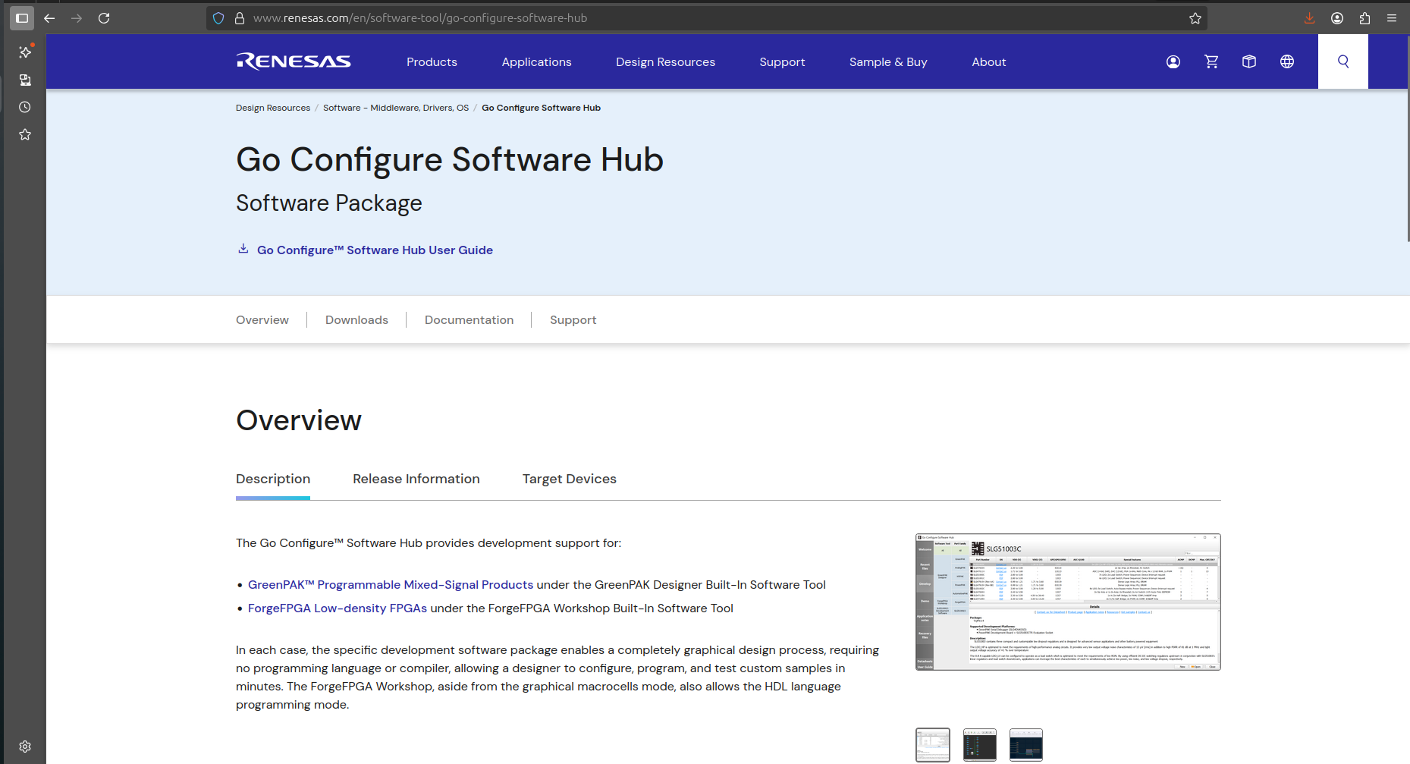
docs/images/tools_setup/goconfig_landing_page.png
