sajeedGIT/shrike_lite_ssm/docs/images/tools_setup/renesas_login.png

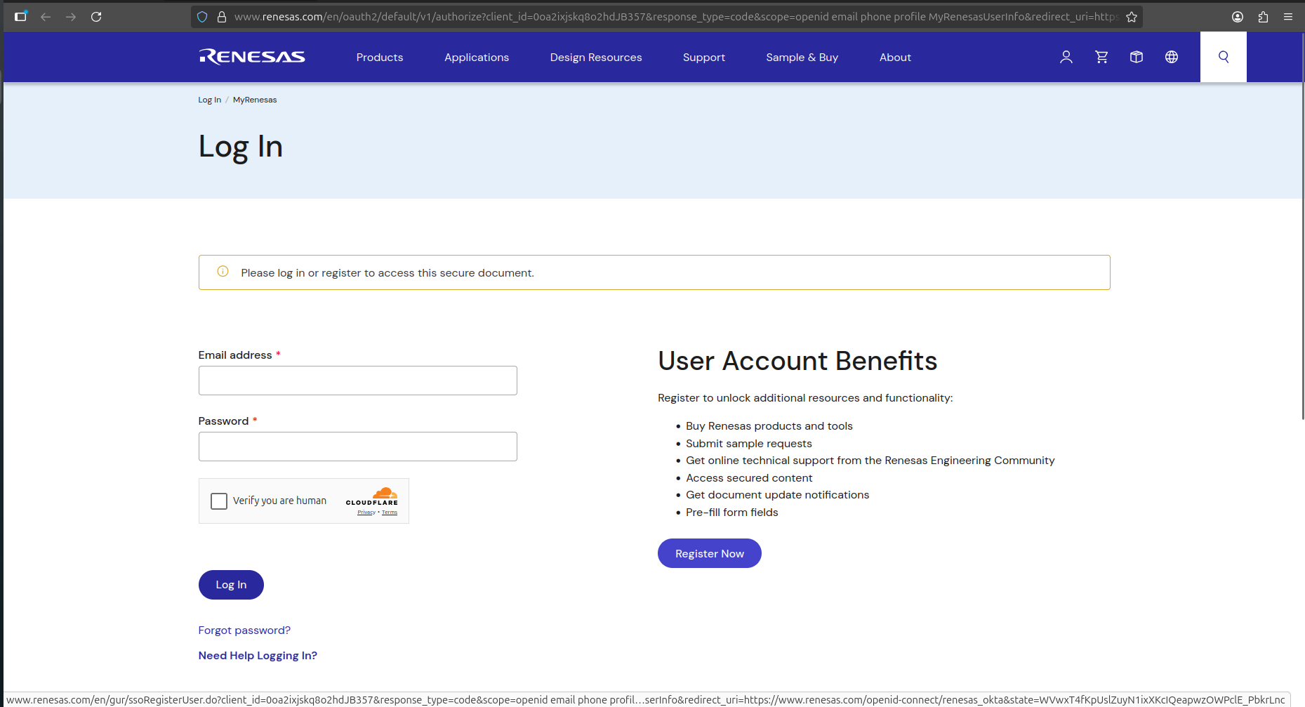
docs/images/tools_setup/renesas_login.png
