sajeedGIT/shrike_lite_ssm/docs/images/tools_setup/software_OS.png

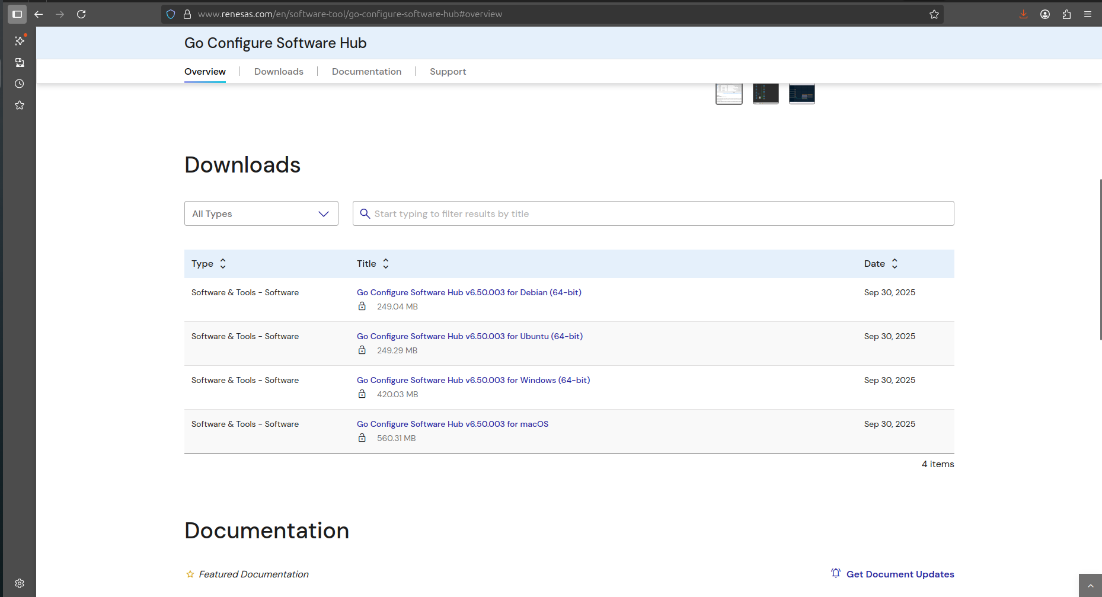
docs/images/tools_setup/software_OS.png
