sajeedGIT/shrike_lite_ssm/docs/images/tools_setup/thonny.png

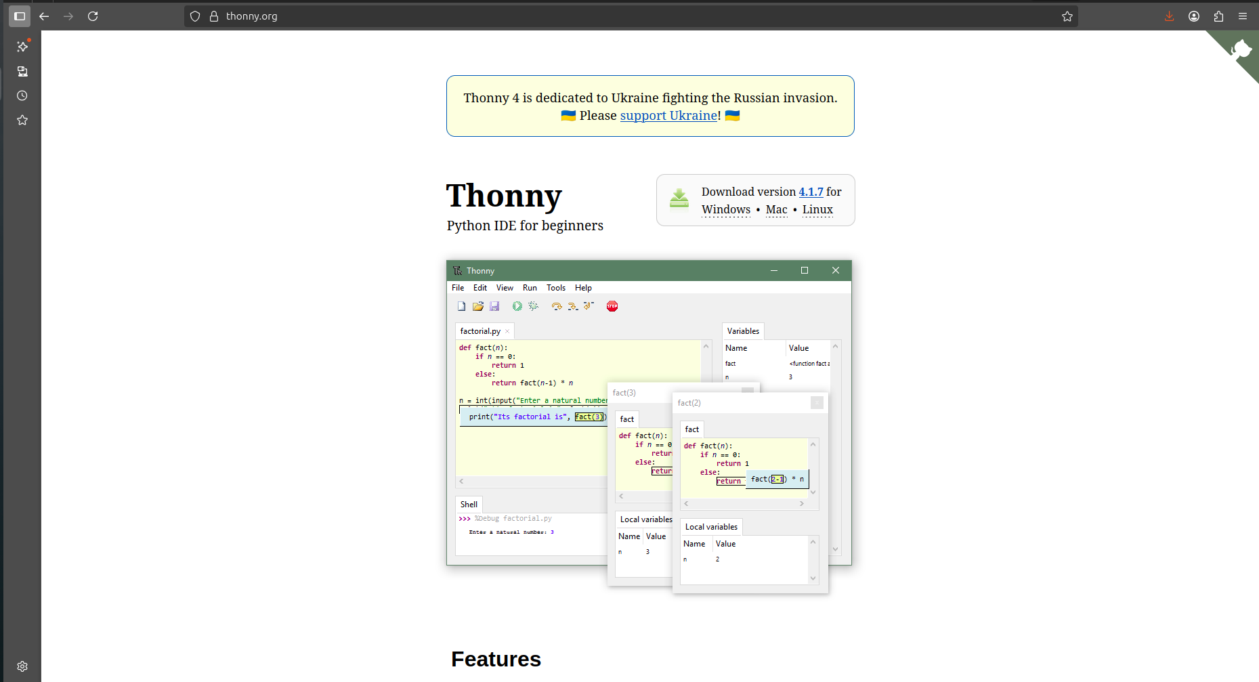
docs/images/tools_setup/thonny.png
