sajeedGIT/shrike_lite_ssm/examples/usb_to_spi/images/hardware_setup.jpeg

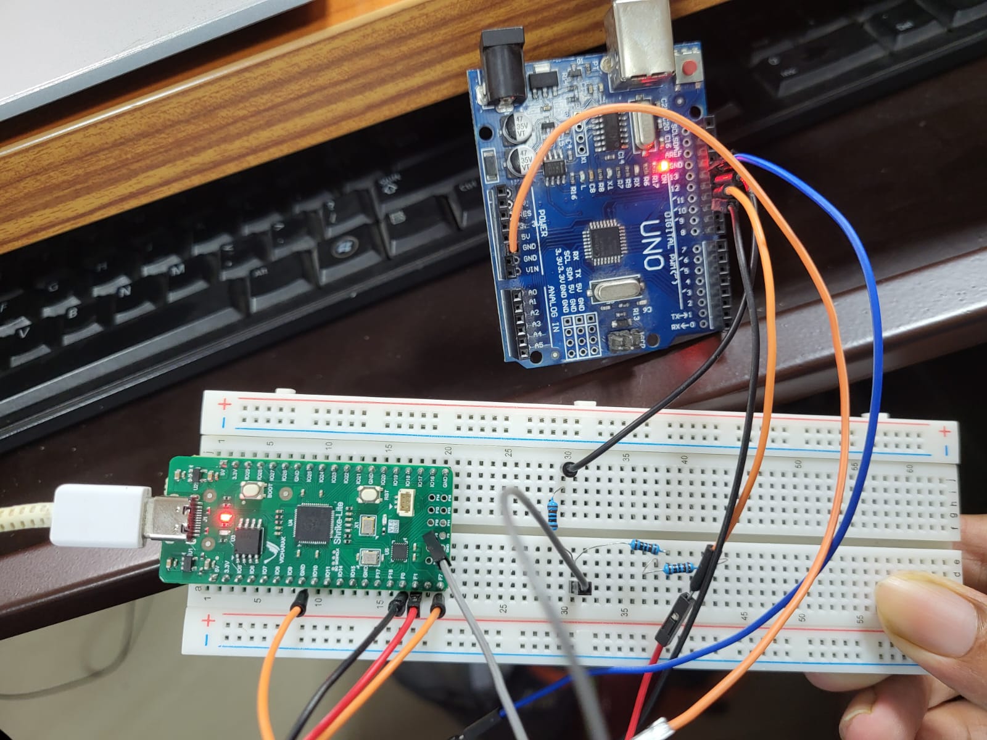
examples/usb_to_spi/images/hardware_setup.jpeg
