sajeedGIT/shrike_lite_ssm/examples/counter_4bit/media/Result.png

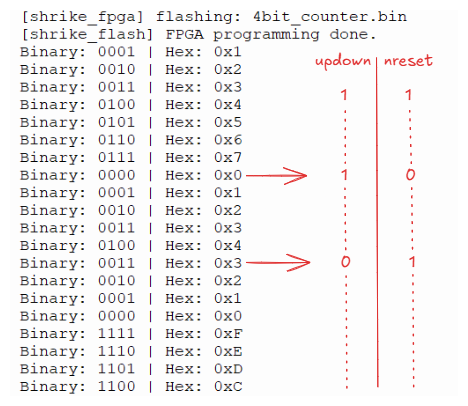
examples/counter_4bit/media/Result.png
