sajeedGIT/shrike_lite_ssm/examples/PSRAM_test/images/output.jpeg

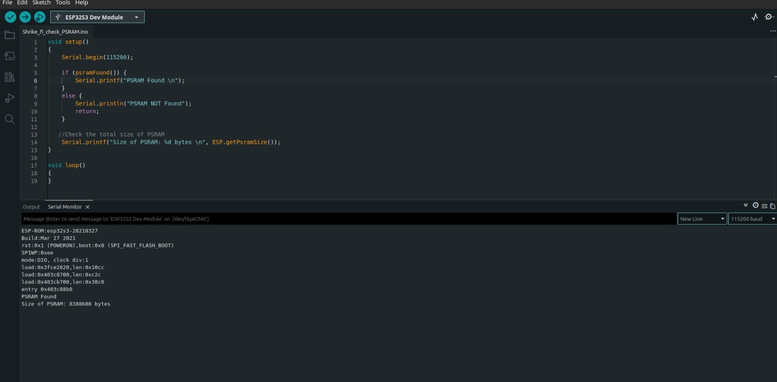
examples/PSRAM_test/images/output.jpeg
