sajeedGIT/shrike_lite_ssm/examples/dspi_pio_echo/ffpga/main.v

// ============================================================================
// TOP MODULE: Dual-SPI Loopback/Echo (Original Control Pins)
// ============================================================================
(* top *) module top ( 
    (* iopad_external_pin, clkbuf_inhibit *) input clk,
    (* iopad_external_pin *)                 output clk_en, 
    
    // SPI Clock
    (* iopad_external_pin *) input  spi_sck, 
    
    // Split CS/IRQ Pins
    (* iopad_external_pin *) input  spi_ss_in,  
    (* iopad_external_pin *) output spi_ss_out, 
    (* iopad_external_pin *) output spi_ss_oe,  
    
    // Split Dual-SPI Data Pins (2 Bits Wide)
    (* iopad_external_pin *) input  [1:0] dual_rx, 
    (* iopad_external_pin *) output [1:0] dual_tx, 
    (* iopad_external_pin *) output [1:0] dual_oe, 

    // Status LED
    (* iopad_external_pin *) output reg led, 
    (* iopad_external_pin *) output led_en 
);

    wire rst_n = 1'b1; 
    assign led_en = 1'b1;
    assign clk_en = 1'b1;

    // --------------------------------------------------------
    // Shared CS/IRQ Logic
    // --------------------------------------------------------
    reg fpga_wants_to_talk = 0;
    assign spi_ss_out = 1'b0; 
    assign spi_ss_oe  = fpga_wants_to_talk; 

    // --------------------------------------------------------
    // THE LOOPBACK: Direct Echo 
    // --------------------------------------------------------
    wire [7:0] rx_data_wire;
    wire       rx_valid_pulse;
    reg  [7:0] tx_data_reg;

    always @(*) begin
        if (fpga_wants_to_talk) begin
            tx_data_reg = 8'hFF; // Alert Code
        end else begin
            tx_data_reg = rx_data_wire; // Echo
        end
    end

    // --------------------------------------------------------
    // Timers (Heartbeat & Interrupt)
    // --------------------------------------------------------
    reg [26:0] timer = 0; 
    reg [24:0] blink_timer = 0; 
    
    always @(posedge clk) begin
        blink_timer <= blink_timer + 1;
        led <= blink_timer[24]; 

        if (rx_valid_pulse || spi_sck) begin
            fpga_wants_to_talk <= 1'b0;
            timer <= 0;
        end else begin
            if (timer == 100_000_000) begin 
                fpga_wants_to_talk <= 1'b1; 
                timer <= timer;             
            end else begin
                timer <= timer + 1;
            end
        end
    end

    // --------------------------------------------------------
    // Target Instantiation
    // --------------------------------------------------------
    dual_spi_target u_target (
        .i_clk(clk),
        .i_rst_n(rst_n),
        .i_ss_n(spi_ss_in),     
        .i_sck(spi_sck),
        .i_dual_rx(dual_rx),
        .o_dual_tx(dual_tx),
        .o_dual_oe(dual_oe),
        .o_rx_data(rx_data_wire),
        .o_rx_data_valid(rx_valid_pulse),
        .i_tx_data(tx_data_reg) 
    );
endmodule

// ============================================================================
// INTERNAL MODULE: Dual-SPI Target FSM
// ============================================================================
module dual_spi_target (
    input  wire       i_clk,
    input  wire       i_rst_n,
    input  wire       i_ss_n,
    input  wire       i_sck,
    
    input  wire [1:0] i_dual_rx,
    output reg  [1:0] o_dual_tx,
    output reg  [1:0] o_dual_oe,
    
    output reg  [7:0] o_rx_data,
    output reg        o_rx_data_valid,
    input  wire [7:0] i_tx_data
);

    localparam STATE_IDLE = 4'd0;
    localparam STATE_RX_1 = 4'd1;
    localparam STATE_RX_2 = 4'd2;
    localparam STATE_RX_3 = 4'd3;
    localparam STATE_RX_4 = 4'd4;
    localparam STATE_TURN = 4'd5;
    localparam STATE_TX_1 = 4'd6;
    localparam STATE_TX_2 = 4'd7;
    localparam STATE_TX_3 = 4'd8;
    localparam STATE_TX_4 = 4'd9;

    reg [3:0] state;

    reg [2:0] sck_sync, cs_sync;
    always @(posedge i_clk or negedge i_rst_n) begin
        if (!i_rst_n) begin
            sck_sync <= 3'b000;
            cs_sync  <= 3'b111;
        end else begin
            sck_sync <= {sck_sync[1:0], i_sck};
            cs_sync  <= {cs_sync[1:0], i_ss_n};
        end
    end

    wire sck_rising = (sck_sync[2:1] == 2'b01);
    wire cs_active  = ~cs_sync[1]; 

    always @(posedge i_clk or negedge i_rst_n) begin
        if (!i_rst_n) begin
            state <= STATE_IDLE;
            o_dual_oe <= 2'b00;
            o_rx_data <= 8'h00;
            o_rx_data_valid <= 1'b0;
            o_dual_tx <= 2'b00;
        end else begin
            o_rx_data_valid <= 1'b0; 

            if (!cs_active) begin
                state <= STATE_IDLE;
                o_dual_oe <= 2'b00; 
            end else if (sck_rising) begin
                case (state)
                    STATE_IDLE: begin state <= STATE_RX_1; o_rx_data[7:6] <= i_dual_rx; end
                    STATE_RX_1: begin state <= STATE_RX_2; o_rx_data[5:4] <= i_dual_rx; end
                    STATE_RX_2: begin state <= STATE_RX_3; o_rx_data[3:2] <= i_dual_rx; end
                    STATE_RX_3: begin state <= STATE_RX_4; o_rx_data[1:0] <= i_dual_rx; end
                    STATE_RX_4: begin
                        state <= STATE_TURN;
                        o_dual_oe <= 2'b11;        
                        o_rx_data_valid <= 1'b1;     
                    end
                    STATE_TURN: begin state <= STATE_TX_1; o_dual_tx <= i_tx_data[7:6]; end
                    STATE_TX_1: begin state <= STATE_TX_2; o_dual_tx <= i_tx_data[5:4]; end
                    STATE_TX_2: begin state <= STATE_TX_3; o_dual_tx <= i_tx_data[3:2]; end
                    STATE_TX_3: begin state <= STATE_TX_4; o_dual_tx <= i_tx_data[1:0]; end
                    STATE_TX_4: begin state <= STATE_IDLE; o_dual_oe <= 2'b00; end
                    default:    begin state <= STATE_IDLE; o_dual_oe <= 2'b00; end
                endcase
            end
        end
    end
endmodule
