sajeedGIT/shrike_lite_ssm/examples/protocol_translator/uart_to_spi_bridge/ffpga/src/spi_master.v

`timescale 1ns/1ps
//------------------------------------------------------------
// Module Name : spi_master
//
// Description:
// Implements an SPI Master for 8-bit data transfer.
//
// Features:
// - SPI Mode 0 (CPOL = 0, CPHA = 0)
// - MSB First Transmission
// - Configurable Clock Divider
// - Full Duplex Communication
//
// SPI Signals:
// SCLK : Serial Clock
// MOSI : Master Out Slave In
// MISO : Master In Slave Out
// CS_N : Chip Select (Active Low)
//
//------------------------------------------------------------

module spi_master#(
    parameter CLK_DIV = 25
)(
    input  wire       clk,
    input  wire       rst,

    input  wire       start,
    input  wire [7:0] tx_data,

    output reg  [7:0] rx_data,
    output reg        done,

    output reg        sclk,
    output reg        mosi,
    output reg        cs_n,
    input  wire       miso
);

    localparam IDLE  = 2'd0;
    localparam SHIFT = 2'd1;
    localparam DONE  = 2'd2;

    reg [1:0] state;
    reg [7:0] tx_shift;
    reg [7:0] rx_shift;
    reg [2:0] bit_cnt;
    reg [7:0] clk_cnt;

    always @(posedge clk or posedge rst) begin
        if(rst) begin
            state    <= IDLE;
            sclk     <= 1'b0;
            cs_n     <= 1'b1;
            mosi     <= 1'b0;
            rx_data  <= 8'd0;
            done     <= 1'b0;
            tx_shift <= 8'd0;
            rx_shift <= 8'd0;
            bit_cnt  <= 3'd0;
            clk_cnt  <= 8'd0;
        end
        else begin
            done <= 1'b0;

            case(state)
                IDLE: begin
                    sclk <= 1'b0;
                    cs_n <= 1'b1;

                    if(start) begin
                        cs_n <= 1'b0;
                        tx_shift <= tx_data;
                        rx_shift <= 8'd0;
                        bit_cnt <= 3'd7;
                        clk_cnt <= 8'd0;
                        mosi <= tx_data[7];
                        state <= SHIFT;
                    end
                end

                SHIFT: begin
                    if(clk_cnt == CLK_DIV-1)  begin
                        clk_cnt <= 0;
                        sclk <= ~sclk;

                        if(sclk == 1'b0) begin
                            rx_shift[bit_cnt] <= miso;
                        end

                        else begin
                            if(bit_cnt == 0) begin
                                state <= DONE;
                            end
                            else begin
                                bit_cnt <= bit_cnt - 1'b1;
                                tx_shift <= {tx_shift[6:0],1'b0};
                                mosi <= tx_shift[6];
                            end
                        end
                    end
                    else begin
                        clk_cnt <= clk_cnt + 1'b1;
                    end

                end

                DONE: begin
                    cs_n <= 1'b1; 
                    sclk <= 1'b0;
                    rx_data <= rx_shift;
                    done <= 1'b1;
                    state <= IDLE;
                end

                default:
                    state <= IDLE;
            endcase

        end
    end

endmodule
