sajeedGIT/shrike_lite_ssm/examples/i2c_led/firmware/micropython/i2c_detect.py

# I2C Scanner MicroPython
from machine import Pin, I2C


#reset pin for active low reset 
# pin value low is reset
reset = machine.Pin(3, machine.Pin.OUT)
reset.high()   


# You can choose any other combination of I2C pins
i2c = I2C(scl=Pin(1), sda=Pin(0))

print('I2C SCANNER')
devices = i2c.scan()

if len(devices) == 0:
  print("No i2c device !")
else:
  print('i2c devices found:', len(devices))

  for device in devices:
    print("I2C hexadecimal address: ", hex(device))
