sajeedGIT/shrike_lite_ssm/examples/protocol_translator/uart_to_spi_bridge/firmware/micropython/uart_to_spi_bridge.py

"""

File Name : uart_to_spi_bridge.py

Description:
MicroPython test program for the UART-to-SPI Bridge.

Sends 100 bytes to the FPGA through UART and
verifies that the same bytes are returned through
the SPI loopback path.

Pin Mapping:

UART:
FPGA GPIO14 (RX) -> UART TX 
FPGA GPIO15 (TX) -> UART RX 

SPI:
FPGA GPIO10 -> SCLK
FPGA GPIO11 -> CS
FPGA GPIO12 -> MOSI
FPGA GPIO13 -> MISO

Test Setup:

* RP2040 UART0 used as UART host
* GP16 connected to FPGA GPIO14 (RX)
* GP17 connected to FPGA GPIO15 (TX)
* FPGA GPIO12 (MOSI) connected to FPGA GPIO13 (MISO) using external jumper

Clock:
SPI Clock = 1 MHz

Baud Rate:
115200

Expected:
TX Byte = RX Byte

---

"""


from machine import UART, Pin
import time

uart = UART(
    0,
    baudrate=115200,
    tx=Pin(16),
    rx=Pin(17)
)

print("UART-SPI LOOPBACK TEST")
print("--------------------------------")

errors = 0

for i in range(100):

    tx_byte = i & 0xFF

    print("Sending  : 0x{:02X}".format(tx_byte))

    uart.write(bytes([tx_byte]))

    time.sleep_ms(100)

    if uart.any():

        rx = uart.read()

        if rx is not None and len(rx) > 0:

            rx_byte = rx[0]

            print("Received : 0x{:02X}".format(rx_byte))

            if rx_byte != tx_byte:
                errors += 1
                print("ERROR")

        else:
            errors += 1
            print("READ ERROR")

    else:
        errors += 1
        print("NO RESPONSE")

print("--------------------------------")
print("Test Complete")
print("Errors =", errors)

if errors == 0:
    print("PASS")
else:
    print("FAIL")
